AndreG-P/AGPKeebo/pcb/AGPKeeb.kicad_sch

## KiCad design pcb/AGPKeeb.kicad_sch (2023-09-22)

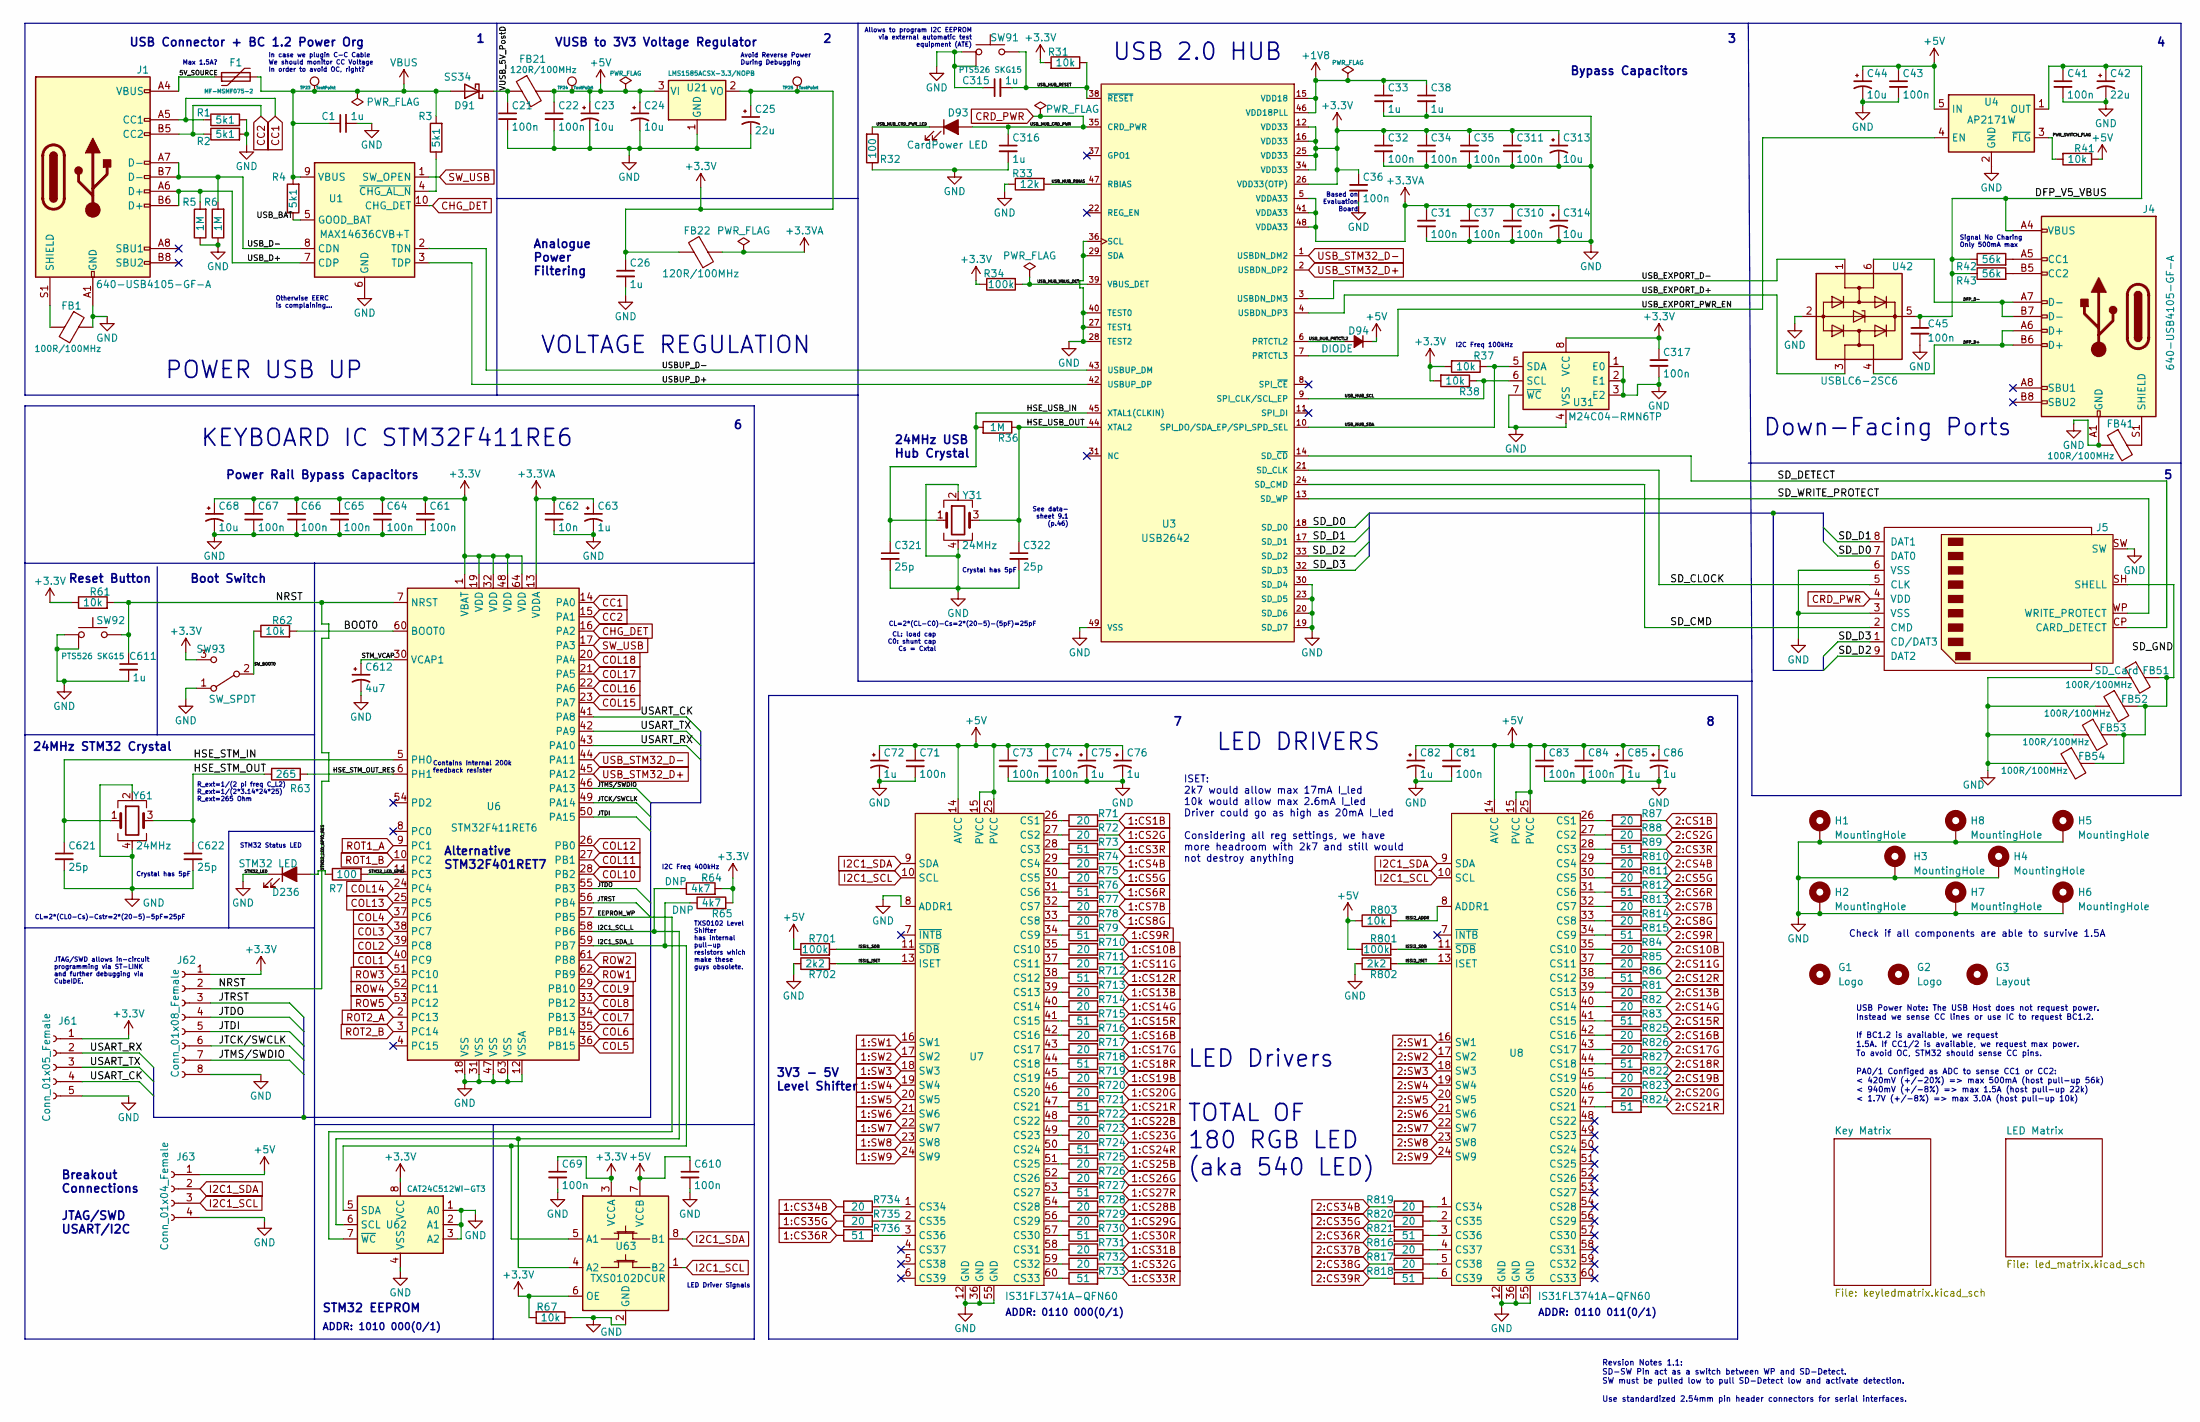
[picture p17: schematic AGPKeeb.kicad_sch]

Parts:
C1, C26, C33, C38, C63, C72, C75, C76, C82, C85, C86, C315, C316, C611: 1u; C_0402_1005Metric; LCSC C52923
C21, C22, C31, C32, C34, C35, C36, C37, C41, C43, C45, C61, C64, C65, C66, C67, C69, C71, C73, C74, C81, C83, C84, C310, C311, C317, C610: 100n; C_0402_1005Metric; LCSC C1525
C23, C24, C44, C68, C313, C314: 10u; CP_EIA-3216-18_Kemet-A; LCSC C7171
C25, C42: 22u; CP_EIA-3216-18_Kemet-A_Pad1.58x1.35mm_HandSolder
C62: 10n; C_0402_1005Metric; LCSC C15195
C321, C322, C621, C622: 25p; C_0603_1608Metric; LCSC C388042
C612: 4u7; CP_EIA-3216-18_Kemet-A_Pad1.58x1.35mm_HandSolder
D91: SS34; D_SMA; LCSC C8678
D93: CardPower LED; Fuse_0603_1608Metric
D94: DIODE; D_SOD-323; LCSC C191023
D236: STM32 LED; Fuse_0603_1608Metric
F1: MF-MSMF075-2; Fuse_1812_4532Metric
FB1, FB41, FB51, FB52, FB53, FB54: 100R/100MHz; L_0805_2012Metric_Pad1.05x1.20mm_HandSolder; LCSC C1015
FB21, FB22: 120R/100MHz; L_0603_1608Metric; LCSC *C113030
G1: Logo; agp-logo
G2: Logo; agp-logo-large
G3: Layout; layout
H1, H2, H3, H4, H5, H6, H7, H8: MountingHole; MountingHole_2.2mm_M2_Pad_Via
J1, J4: 640-USB4105-GF-A; USB_C_Receptacle_GCT_USB4105-xx-A_16P_TopMnt_Horizontal
J5: SD_Card; SD_Hirose_DM1AA_SF_PEJ82
J61: Conn_01x05_Female; JST_SH_SM05B-SRSS-TB_1x05-1MP_P1.00mm_Horizontal
J62: Conn_01x08_Female; JST_SH_SM08B-SRSS-TB_1x08-1MP_P1.00mm_Horizontal
J63: Conn_01x04_Female; JST_SH_SM04B-SRSS-TB_1x04-1MP_P1.00mm_Horizontal
R1, R2, R3, R4: 5k1; R_0402_1005Metric; LCSC C25905
R5, R6, R36: 1M; R_0402_1005Metric; LCSC C26083
R7, R32: 100; R_0402_1005Metric; LCSC C25076
R31, R37, R38, R41, R61, R62, R67, R803: 10k; R_0402_1005Metric; LCSC C25744
R33: 12k; R_0402_1005Metric; LCSC C25752
R34, R701, R801: 100k; R_0402_1005Metric; LCSC C25741
R42, R43: 56k; R_0402_1005Metric; LCSC C25796
R63: 265; R_0402_1005Metric; LCSC C11543
R64, R65: 4k7; R_0402_1005Metric
R71, R72, R74, R75, R77, R78, R81, R82, R84, R85, R87, R88, R710, R711, R713, R714, R716, R717, R719, R720, R722, R723, R725, R726, R728, R729, R731, R732, R734, R735, R810, R811, R813, R814, R816, R817, R819, R820, R822, R823, R825, R826: 20; R_0402_1005Metric; LCSC C25089
R73, R76, R79, R83, R86, R89, R712, R715, R718, R721, R724, R727, R730, R733, R736, R812, R815, R818, R821, R824, R827: 51; R_0402_1005Metric; LCSC C25125
R702, R802: 2k2; R_0402_1005Metric; LCSC C25879
SW91, SW92: PTS526 SKG15; SW_SPST_PTS526; LCSC *C2800943
SW93: SW_SPDT; SW_SPDT_PCM12; LCSC *C109335
TP23, TP24, TP25: TestPoint; TestPoint_Pad_D1.0mm
U1: MAX14636CVB+T; UTQFN-10_1.6x2.1mm_P0.5mm
U3: USB2642; Microchip_Technology-48QFN-5304-7x7B-07_2007-B-MFG
U4: AP2171W; SOT-23-5; LCSC *C110466
U6: STM32F411RET6; LQFP-64_10x10mm_P0.5mm; LCSC C94355
U7, U8: IS31FL3741A-QFN60; QFN-60-1EP_7x7mm_P0.4_EP5x5mm_ThermalVias; LCSC *C2940604
U21: LMS1585ACSX-3.3/NOPB; TO-252-3_TabPin2
U31: M24C04-RMN6TP; SOIC-8_3.9x4.9mm_P1.27mm; LCSC *C118280
U42: USBLC6-2SC6; SOT-23-6; LCSC *C2827654
U62: CAT24C512WI-GT3; SOIC-8_3.9x4.9mm_P1.27mm; LCSC *C79986
U63: TXS0102DCUR; VSSOP-8_2.3x2mm_P0.5mm; LCSC *C53434
Y31, Y61: 24MHz; Crystal_SMD_TXC_7M-4Pin_3.2x2.5mm; LCSC *C164048

Connections:
1:CS1B: R71.2
1:CS2G: R72.2
1:CS3R: R73.2
1:CS4B: R74.2
1:CS5G: R75.2
1:CS6R: R76.2
1:CS7B: R77.2
1:CS8G: R78.2
1:CS9R: R79.2
1:CS10B: R710.2
1:CS11G: R711.2
1:CS12R: R712.2
1:CS13B: R713.2
1:CS14G: R714.2
1:CS15R: R715.2
1:CS16B: R716.2
1:CS17G: R717.2
1:CS18R: R718.2
1:CS19B: R719.2
1:CS20G: R720.2
1:CS21R: R721.2
1:CS22B: R722.2
1:CS23G: R723.2
1:CS24R: R724.2
1:CS25B: R725.2
1:CS26G: R726.2
1:CS27R: R727.2
1:CS28B: R728.2
1:CS29G: R729.2
1:CS30R: R730.2
1:CS31B: R731.2
1:CS32G: R732.2
1:CS33R: R733.2
1:CS34B: R734.1
1:CS35G: R735.1
1:CS36R: R736.1
1:SW1: U7.16 (SW1)
1:SW2: U7.17 (SW2)
1:SW3: U7.18 (SW3)
1:SW4: U7.19 (SW4)
1:SW5: U7.20 (SW5)
1:SW6: U7.21 (SW6)
1:SW7: U7.22 (SW7)
1:SW8: U7.23 (SW8)
1:SW9: U7.24 (SW9)
2:CS1B: R87.2
2:CS2G: R88.2
2:CS3R: R89.2
2:CS4B: R810.2
2:CS5G: R811.2
2:CS6R: R812.2
2:CS7B: R813.2
2:CS8G: R814.2
2:CS9R: R815.2
2:CS10B: R84.2
2:CS11G: R85.2
2:CS12R: R86.2
2:CS13B: R81.2
2:CS14G: R82.2
2:CS15R: R83.2
2:CS16B: R825.2
2:CS17G: R826.2
2:CS18R: R827.2
2:CS19B: R822.2
2:CS20G: R823.2
2:CS21R: R824.2
2:CS34B: R819.2
2:CS35G: R820.2
2:CS36R: R821.2
2:CS37B: R816.2
2:CS38G: R817.2
2:CS39R: R818.2
2:SW1: U8.16 (SW1)
2:SW2: U8.17 (SW2)
2:SW3: U8.18 (SW3)
2:SW4: U8.19 (SW4)
2:SW5: U8.20 (SW5)
2:SW6: U8.21 (SW6)
2:SW7: U8.22 (SW7)
2:SW8: U8.23 (SW8)
2:SW9: U8.24 (SW9)
5V_SOURCE: F1.1, J1.A4 (VBUS), J1.A9 (VBUS), J1.B4 (VBUS), J1.B9 (VBUS)
+1V8: C33.1, C38.1, U3.15 (VDD18), U3.46 (VDD18PLL)
+3.3V: C25.1, C26.1, C32.1, C34.1, C35.1, C36.1, C61.1, C64.1, C65.1, C66.1, C67.1, C68.1, C69.1, C311.1, C313.1, C317.1, FB22.2, J61.1, J62.1, R31.2, R34.1, R37.2, R38.2, R61.1, R64.2, R65.2, R67.2, SW93.3 (C), TP25.1, U3.12 (VDD33), U3.16 (VDD33), U3.25 (VDD33), U3.26 (VDD33(OTP)), U3.34 (VDD33), U6.1 (VBAT), U6.19 (VDD), U6.32 (VDD), U6.48 (VDD), U6.64 (VDD), U21.2 (VO), U31.8 (VCC), U62.8 (VCC), U63.3 (VCCA), U63.6 (OE)
+3.3VA: C31.1, C37.1, C62.1, C63.1, C310.1, C314.1, FB22.1, U3.5 (VDDA33), U3.41 (VDDA33), U3.48 (VDDA33), U6.13 (VDDA)
+5V: C22.1, C23.1, C24.1, C43.1, C44.1, C71.1, C72.1, C73.1, C74.1, C75.1, C76.1, C81.1, C82.1, C83.1, C84.1, C85.1, C86.1, C610.1, D94.1 (K), FB21.2, J63.1, R41.1, R701.1, R801.1, R803.1, TP24.1, U4.5 (IN), U7.14 (AVCC), U7.15 (PVCC), U7.25 (PVCC), U8.14 (AVCC), U8.15 (PVCC), U8.25 (PVCC), U21.3 (VI), U63.7 (VCCB)
BOOT0: R62.2, U6.60 (BOOT0)
CC1: J1.A5 (CC1), R1.1, U6.14 (PA0)
CC2: J1.B5 (CC2), R2.1, U6.15 (PA1)
CHG_DET: U1.10 (CHG_DET), U6.16 (PA2)
COL1: U6.40 (PC9)
COL2: U6.39 (PC8)
COL3: U6.38 (PC7)
COL4: U6.37 (PC6)
COL5: U6.36 (PB15)
COL6: U6.35 (PB14)
COL7: U6.34 (PB13)
COL8: U6.33 (PB12)
COL9: U6.29 (PB10)
COL10: U6.28 (PB2)
COL11: U6.27 (PB1)
COL12: U6.26 (PB0)
COL13: U6.25 (PC5)
COL14: U6.24 (PC4)
COL15: U6.23 (PA7)
COL16: U6.22 (PA6)
COL17: U6.21 (PA5)
COL18: U6.20 (PA4)
CRD_PWR: C316.1, D93.2 (A), J5.4 (VDD), U3.35 (CRD_PWR)
DFP_D+: J4.A6 (D+), J4.B6 (D+), U42.4 (I/O2)
DFP_D-: J4.A7 (D-), J4.B7 (D-), U42.6 (I/O1)
DFP_V5_VBUS: C41.1, C42.1, C45.1, J4.A4 (VBUS), J4.A9 (VBUS), J4.B4 (VBUS), J4.B9 (VBUS), R42.1, R43.1, U4.1 (OUT), U42.5 (VBUS)
EEPROM_WP: U6.57 (PB5), U62.7 (~WC)
GND: C1.2, C21.2, C22.2, C23.2, C24.2, C25.2, C26.2, C31.2, C32.2, C33.2, C34.2, C35.2, C36.2, C37.2, C38.2, C41.2, C42.2, C43.2, C44.2, C45.2, C61.2, C62.2, C63.2, C64.2, C65.2, C66.2, C67.2, C68.2, C69.2, C71.2, C72.2, C73.2, C74.2, C75.2, C76.2, C81.2, C82.2, C83.2, C84.2, C85.2, C86.2, C310.2, C311.2, C313.2, C314.2, C315.1, C316.2, C317.2, C321.2, C322.2, C610.2, C611.2, C612.2, C621.2, C622.2, D236.1 (K), FB1.1, FB41.1, FB51.1, FB52.1, FB53.1, FB54.1, H1.1, H2.1, H3.1, H4.1, H5.1, H6.1, H7.1, H8.1, J1.A1 (GND), J1.A12 (GND), J1.B1 (GND), J1.B12 (GND), J4.A1 (GND), J4.A12 (GND), J4.B1 (GND), J4.B12 (GND), J5.3 (VSS), J5.6 (VSS), J5.SW, J61.5, J62.8, J63.4, R1.2, R2.2, R5.1, R6.1, R32.1, R33.1, R67.1, R702.1, R802.1, SW91.1, SW91.3 (GND), SW92.1, SW92.3 (GND), SW93.1 (A), U1.6 (GND), U3.19 (SD_D7), U3.20 (SD_D6), U3.23 (SD_D5), U3.27 (TEST1), U3.28 (TEST2), U3.29 (SDA), U3.30 (SD_D4), U3.36 (SCL), U3.40 (TEST0), U3.49 (VSS), U4.2 (GND), U6.12 (VSSA), U6.18 (VSS), U6.31 (VSS), U6.47 (VSS), U6.63 (VSS), U7.8 (ADDR1), U7.12 (GND), U7.36 (GND), U7.55 (GND), U7.61 (PGND), U8.12 (GND), U8.36 (GND), U8.55 (GND), U8.61 (PGND), U21.1 (GND), U31.1 (E0), U31.2 (E1), U31.3 (E2), U31.4 (VSS), U31.7 (~WC), U42.2 (GND), U62.1 (A0), U62.2 (A1), U62.3 (A2), U62.4 (VSS), U63.2 (GND), Y31.2, Y31.4, Y61.2, Y61.4
HSE_STM_IN: C621.1, U6.5 (PH0), Y61.1
HSE_STM_OUT: C622.1, R63.1, Y61.3
HSE_STM_OUT_RES: R63.2, U6.6 (PH1)
HSE_USB_IN: C321.1, R36.2, U3.45 (XTAL1(CLKIN)), Y31.1
HSE_USB_OUT: C322.1, R36.1, U3.44 (XTAL2), Y31.3
I2C1_SCL: J63.3, U7.10 (SCL), U8.10 (SCL), U63.1 (B2)
I2C1_SCL_L: R64.1, U6.58 (PB6), U62.6 (SCL), U63.4 (A2)
I2C1_SDA: J63.2, U7.9 (SDA), U8.9 (SDA), U63.8 (B1)
I2C1_SDA_L: R65.1, U6.59 (PB7), U62.5 (SDA), U63.5 (A1)
ISSI1_ISET: R702.2, U7.13 (ISET)
ISSI1_SDB: R701.2, U7.11 (~SDB)
ISSI2_ADDR: R803.2, U8.8 (ADDR1)
ISSI2_ISET: R802.2, U8.13 (ISET)
ISSI2_SDB: R801.2, U8.11 (~SDB)
JTCK/SWCLK: J62.6, U6.49 (PA14)
JTDI: J62.5, U6.50 (PA15)
JTDO: J62.4, U6.55 (PB3)
JTMS/SWDIO: J62.7, U6.46 (PA13)
JTRST: J62.3, U6.56 (PB4)
NRST: C611.1, J62.2, R61.2, SW92.2, U6.7 (NRST)
unnamed: FB1.2, J1.S1 (SHIELD)
unnamed: FB41.2, J4.S1 (SHIELD)
unnamed: J4.A5 (CC1), R42.2
unnamed: J4.B5 (CC2), R43.2
unnamed: R3.1, U1.4 (~CHG_AL_N)
unnamed: R71.1, U7.26 (CS1)
unnamed: R72.1, U7.27 (CS2)
unnamed: R73.1, U7.28 (CS3)
unnamed: R74.1, U7.29 (CS4)
unnamed: R75.1, U7.30 (CS5)
unnamed: R76.1, U7.31 (CS6)
unnamed: R77.1, U7.32 (CS7)
unnamed: R78.1, U7.33 (CS8)
unnamed: R79.1, U7.34 (CS9)
unnamed: R81.1, U8.39 (CS13)
unnamed: R82.1, U8.40 (CS14)
unnamed: R83.1, U8.41 (CS15)
unnamed: R84.1, U8.35 (CS10)
unnamed: R85.1, U8.37 (CS11)
unnamed: R86.1, U8.38 (CS12)
unnamed: R87.1, U8.26 (CS1)
unnamed: R88.1, U8.27 (CS2)
unnamed: R89.1, U8.28 (CS3)
unnamed: R710.1, U7.35 (CS10)
unnamed: R711.1, U7.37 (CS11)
unnamed: R712.1, U7.38 (CS12)
unnamed: R713.1, U7.39 (CS13)
unnamed: R714.1, U7.40 (CS14)
unnamed: R715.1, U7.41 (CS15)
unnamed: R716.1, U7.42 (CS16)
unnamed: R717.1, U7.43 (CS17)
unnamed: R718.1, U7.44 (CS18)
unnamed: R719.1, U7.45 (CS19)
unnamed: R720.1, U7.46 (CS20)
unnamed: R721.1, U7.47 (CS21)
unnamed: R722.1, U7.48 (CS22)
unnamed: R723.1, U7.49 (CS23)
unnamed: R724.1, U7.50 (CS24)
unnamed: R725.1, U7.51 (CS25)
unnamed: R726.1, U7.52 (CS26)
unnamed: R727.1, U7.53 (CS27)
unnamed: R728.1, U7.54 (CS28)
unnamed: R729.1, U7.56 (CS29)
unnamed: R730.1, U7.57 (CS30)
unnamed: R731.1, U7.58 (CS31)
unnamed: R732.1, U7.59 (CS32)
unnamed: R733.1, U7.60 (CS33)
unnamed: R734.2, U7.1 (CS34)
unnamed: R735.2, U7.2 (CS35)
unnamed: R736.2, U7.3 (CS36)
unnamed: R810.1, U8.29 (CS4)
unnamed: R811.1, U8.30 (CS5)
unnamed: R812.1, U8.31 (CS6)
unnamed: R813.1, U8.32 (CS7)
unnamed: R814.1, U8.33 (CS8)
unnamed: R815.1, U8.34 (CS9)
unnamed: R816.1, U8.4 (CS37)
unnamed: R817.1, U8.5 (CS38)
unnamed: R818.1, U8.6 (CS39)
unnamed: R819.1, U8.1 (CS34)
unnamed: R820.1, U8.2 (CS35)
unnamed: R821.1, U8.3 (CS36)
unnamed: R822.1, U8.45 (CS19)
unnamed: R823.1, U8.46 (CS20)
unnamed: R824.1, U8.47 (CS21)
unnamed: R825.1, U8.42 (CS16)
unnamed: R826.1, U8.43 (CS17)
unnamed: R827.1, U8.44 (CS18)
PWR_SWITCH_FLAG: R41.2, U4.3 (~FLG)
ROT1_A: U6.9 (PC1)
ROT1_B: U6.10 (PC2)
ROT2_A: U6.2 (PC13)
ROT2_B: U6.3 (PC14)
ROW1: U6.62 (PB9)
ROW2: U6.61 (PB8)
ROW3: U6.51 (PC10)
ROW4: U6.52 (PC11)
ROW5: U6.53 (PC12)
SD_CLOCK: J5.5 (CLK), U3.21 (SD_CLK)
SD_CMD: J5.2 (CMD), U3.24 (SD_CMD)
SD_D0: J5.7 (DAT0), U3.18 (SD_D0)
SD_D1: J5.8 (DAT1), U3.17 (SD_D1)
SD_D2: J5.9 (DAT2), U3.33 (SD_D2)
SD_D3: J5.1 (CD/DAT3), U3.32 (SD_D3)
SD_DETECT: J5.CP (CARD_DETECT), U3.14 (SD_~CD)
SD_GND: FB51.2, FB52.2, FB53.2, FB54.2, J5.SH (SHELL)
SD_WRITE_PROTECT: J5.WP (WRITE_PROTECT), U3.13 (SD_WP)
STM32_LED_GPIO: R7.2, U6.11 (PC3)
STM32_LED_GPIO_RES: D236.2 (A), R7.1
STM_VCAP: C612.1, U6.30 (VCAP1)
SW_BOOT0: R62.1, SW93.2 (B)
SW_USB: U1.1 (SW_OPEN), U6.17 (PA3)
USART_CK: J61.4, U6.41 (PA8)
USART_RX: J61.2, U6.43 (PA10)
USART_TX: J61.3, U6.42 (PA9)
USBUP_D+: U1.3 (TDP), U3.42 (USBUP_DP)
USBUP_D-: U1.2 (TDN), U3.43 (USBUP_DM)
USB_BAT: R4.1, U1.5 (GOOD_BAT)
USB_D+: J1.A6 (D+), J1.B6 (D+), R5.2, U1.7 (CDP)
USB_D-: J1.A7 (D-), J1.B7 (D-), R6.2, U1.8 (CDN)
USB_EXPORT_D+: U3.4 (USBDN_DP3), U42.3 (I/O2)
USB_EXPORT_D-: U3.3 (USBDN_DM3), U42.1 (I/O1)
USB_EXPORT_PWR_EN: U3.7 (PRTCTL3), U4.4 (EN)
USB_HUB_CRD_PWR_LED: D93.1 (K), R32.2
USB_HUB_PRTCTL2: D94.2 (A), U3.6 (PRTCTL2)
USB_HUB_RBIAS: R33.2, U3.47 (RBIAS)
USB_HUB_RESET: C315.2, R31.1, SW91.2, U3.38 (~RESET)
USB_HUB_SCL: R38.1, U3.9 (SPI_CLK/SCL_EP), U31.6 (SCL)
USB_HUB_SDA: R37.1, U3.10 (SPI_DO/SDA_EP/SPI_SPD_SEL), U31.5 (SDA)
USB_HUB_VBUS_DET: R34.2, U3.39 (VBUS_DET)
USB_STM32_D+: U3.2 (USBDN_DP2), U6.45 (PA12)
USB_STM32_D-: U3.1 (USBDN_DM2), U6.44 (PA11)
VBUS: C1.1, D91.2 (A), F1.2, R3.2, R4.2, TP23.1, U1.9 (VBUS)
VUSB_5V_PostD: C21.1, D91.1 (K), FB21.1

Notes on the sheet:
Boot Switch
Contains Internal 200k feedback resister
I2C Freq 100kHz
Crystal has 5pF
LED Driver Signals
JTAG/SWD allows in-circuit programming via ST-LINK and further debugging via CubeIDE.
VUSB to 3V3 Voltage Regulator
3V3 - 5V Level Shifter
In case we plugin C-C Cable We should monitor CC Voltage In order to avoid OC, right?
CL=2*(CL0-Cs)-Cstr=2*(20-5)-5pF=25pF
ADDR: 1010 000(0/1)
24MHz USB Hub Crystal
ADDR: 0110 000(0/1)
CL: load cap C0: shunt cap Cs = Cxtal
Reset Button
VOLTAGE REGULATION
Max 1.5A?
Breakout Connections JTAG/SWD USART/I2C
TXS0102 Level Shifter has internal pull-up resistors which make these guys obsolete.
CL=2*(CL-C0)-Cs=2*(20-5)-(5pF)=25pF
ISET: 2k7 would allow max 17mA I_led 10k would allow max 2.6mA I_led Driver could go as high as 20mA I_led Considering all reg settings, we have more headroom with 2k7 and still would not destroy anything
STM32 EEPROM
I2C Freq 400kHz
Power Rail Bypass Capacitors
Bypass Capacitors
24MHz STM32 Crystal
KEYBOARD IC STM32F411RE6
Analogue Power Filtering
See data- sheet 9.1 (p.46)
ADDR: 0110 011(0/1)
USB 2.0 HUB
USB Connector + BC 1.2 Power Org
Down-Facing Ports
Revsion Notes 1.1: SD-SW Pin act as a switch between WP and SD-Detect. SW must be pulled low to pull SD-Detect low and activate detection. Use standardized 2.54mm pin header connectors for serial interfaces.
Check if all components are able to survive 1.5A
R_ext=1/(2 pi freq C_L2) R_ext=1/(2*3.14*24*25) R_ext=265 Ohm
Avoid Reverse Power During Debugging
STM32 Status LED
Signal No Charing Only 500mA max
LED DRIVERS
Alternative STM32F401RET7
POWER USB UP
USB Power Note: The USB Host does not request power. Instead we sense CC lines or use IC to request BC1.2. If BC1.2 is available, we request 1.5A. If CC1/2 is available, we request max power. To avoid OC, STM32 should sense CC pins. PA0/1 Configed as ADC to sense CC1 or CC2: < 420mV (+/-20%) => max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
LED Drivers TOTAL OF 180 RGB LED (aka 540 LED)
Allows to program I2C EEPROM via external automatic test equipment (ATE)
Otherwise EERC is complaining...
Based on Evaluation Board
