AndreG-P/AGPKeebo/pcb/keyledmatrix.kicad_sch

## KiCad design pcb/keyledmatrix.kicad_sch (2023-09-22)

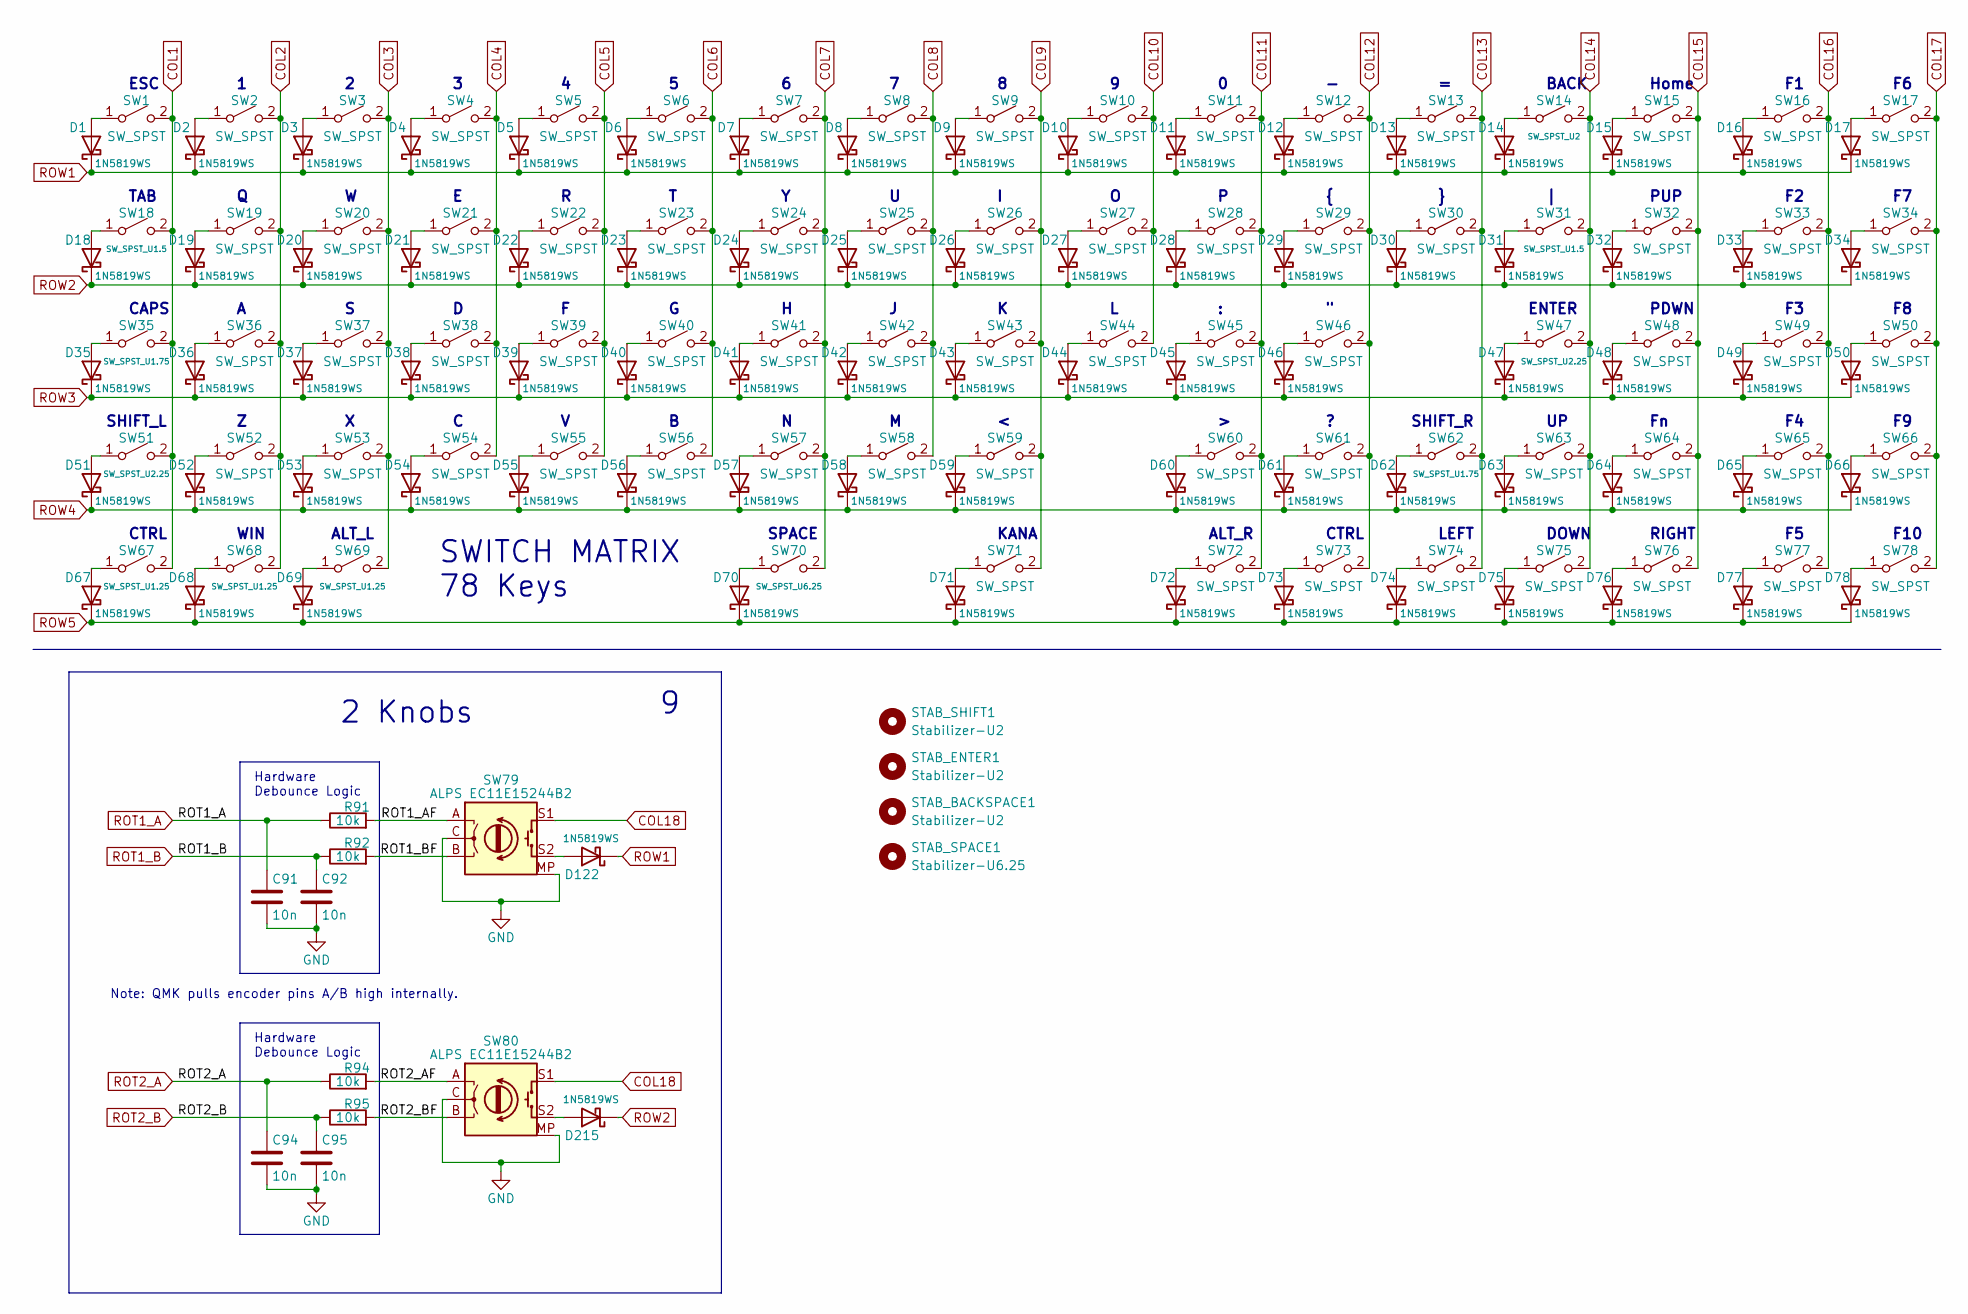
[picture p18: schematic keyledmatrix.kicad_sch]

Parts:
C91, C92, C94, C95: 10n; C_0402_1005Metric; LCSC C15195
D1, D2, D3, D4, D5, D6, D7, D8, D9, D10, D11, D12, D13, D14, D15, D16, D17, D18, D19, D20, D21, D22, D23, D24, D25, D26, D27, D28, D29, D30, D31, D32, D33, D34, D35, D36, D37, D38, D39, D40, D41, D42, D43, D44, D45, D46, D47, D48, D49, D50, D51, D52, D53, D54, D55, D56, D57, D58, D59, D60, D61, D62, D63, D64, D65, D66, D67, D68, D69, D70, D71, D72, D73, D74, D75, D76, D77, D78, D122, D215: 1N5819WS; D_SOD-323; LCSC C191023
R91, R92, R94, R95: 10k; R_0402_1005Metric; LCSC C25744
STAB_BACKSPACE1: Stabilizer-U2; Stabilizer_Cherry_MX_2.00u
STAB_ENTER1: Stabilizer-U2; Stabilizer_Cherry_MX_2.00u
STAB_SHIFT1: Stabilizer-U2; Stabilizer_Cherry_MX_2.00u
STAB_SPACE1: Stabilizer-U6.25; Stabilizer_Cherry_MX_6.25u
SW1, SW2, SW3, SW4, SW5, SW6, SW7, SW8, SW9, SW10, SW11, SW12, SW13, SW15, SW16, SW17, SW19, SW20, SW21, SW22, SW23, SW24, SW25, SW26, SW27, SW28, SW29, SW30, SW32, SW33, SW34, SW36, SW37, SW38, SW39, SW40, SW41, SW42, SW43, SW44, SW45, SW46, SW48, SW49, SW50, SW52, SW53, SW54, SW55, SW56, SW57, SW58, SW59, SW60, SW61, SW63, SW64, SW65, SW66, SW71, SW72, SW73, SW74, SW75, SW76, SW77, SW78: SW_SPST; SW_Hotswap_Kailh_MX_plated_1.00u_clear
SW14: SW_SPST_U2; SW_Hotswap_Kailh_MX_plated_2.00u_clear
SW18, SW31: SW_SPST_U1.5; SW_Hotswap_Kailh_MX_plated_1.50u_clear
SW35, SW62: SW_SPST_U1.75; SW_Hotswap_Kailh_MX_plated_1.75u_clear
SW47, SW51: SW_SPST_U2.25; SW_Hotswap_Kailh_MX_plated_2.25u_clear
SW67, SW68, SW69: SW_SPST_U1.25; SW_Hotswap_Kailh_MX_plated_1.25u_clear
SW70: SW_SPST_U6.25; SW_Hotswap_Kailh_MX_plated_6.25u_clear
SW79, SW80: ALPS EC11E15244B2; RotaryEncoder_Alps_EC11E-Switch_Vertical_H20mm; LCSC *C470754

Connections:
COL1: SW1.2 (B), SW18.2 (B), SW35.2 (B), SW51.2 (B), SW67.2 (B)
COL2: SW2.2 (B), SW19.2 (B), SW36.2 (B), SW52.2 (B), SW68.2 (B)
COL3: SW3.2 (B), SW20.2 (B), SW37.2 (B), SW53.2 (B), SW69.2 (B)
COL4: SW4.2 (B), SW21.2 (B), SW38.2 (B), SW54.2 (B)
COL5: SW5.2 (B), SW22.2 (B), SW39.2 (B), SW55.2 (B)
COL6: SW6.2 (B), SW23.2 (B), SW40.2 (B), SW56.2 (B)
COL7: SW7.2 (B), SW24.2 (B), SW41.2 (B), SW57.2 (B), SW70.2 (B)
COL8: SW8.2 (B), SW25.2 (B), SW42.2 (B), SW58.2 (B)
COL9: SW9.2 (B), SW26.2 (B), SW43.2 (B), SW59.2 (B), SW71.2 (B)
COL10: SW10.2 (B), SW27.2 (B), SW44.2 (B)
COL11: SW11.2 (B), SW28.2 (B), SW45.2 (B), SW60.2 (B), SW72.2 (B)
COL12: SW12.2 (B), SW29.2 (B), SW46.2 (B), SW61.2 (B), SW73.2 (B)
COL13: SW13.2 (B), SW30.2 (B), SW62.2 (B), SW74.2 (B)
COL14: SW14.2 (B), SW31.2 (B), SW47.2 (B), SW63.2 (B), SW75.2 (B)
COL15: SW15.2 (B), SW32.2 (B), SW48.2 (B), SW64.2 (B), SW76.2 (B)
COL16: SW16.2 (B), SW33.2 (B), SW49.2 (B), SW65.2 (B), SW77.2 (B)
COL17: SW17.2 (B), SW34.2 (B), SW50.2 (B), SW66.2 (B), SW78.2 (B)
COL18: SW79.S1, SW80.S1
GND: C91.2, C92.2, C94.2, C95.2, SW79.C, SW79.MP (Shell), SW80.C, SW80.MP (Shell)
unnamed: D1.2 (A), SW1.1 (A)
unnamed: D2.2 (A), SW2.1 (A)
unnamed: D3.2 (A), SW3.1 (A)
unnamed: D4.2 (A), SW4.1 (A)
unnamed: D5.2 (A), SW5.1 (A)
unnamed: D6.2 (A), SW6.1 (A)
unnamed: D7.2 (A), SW7.1 (A)
unnamed: D8.2 (A), SW8.1 (A)
unnamed: D9.2 (A), SW9.1 (A)
unnamed: D10.2 (A), SW10.1 (A)
unnamed: D11.2 (A), SW11.1 (A)
unnamed: D12.2 (A), SW12.1 (A)
unnamed: D13.2 (A), SW13.1 (A)
unnamed: D14.2 (A), SW14.1 (A)
unnamed: D15.2 (A), SW15.1 (A)
unnamed: D16.2 (A), SW16.1 (A)
unnamed: D17.2 (A), SW17.1 (A)
unnamed: D18.2 (A), SW18.1 (A)
unnamed: D19.2 (A), SW19.1 (A)
unnamed: D20.2 (A), SW20.1 (A)
unnamed: D21.2 (A), SW21.1 (A)
unnamed: D22.2 (A), SW22.1 (A)
unnamed: D23.2 (A), SW23.1 (A)
unnamed: D24.2 (A), SW24.1 (A)
unnamed: D25.2 (A), SW25.1 (A)
unnamed: D26.2 (A), SW26.1 (A)
unnamed: D27.2 (A), SW27.1 (A)
unnamed: D28.2 (A), SW28.1 (A)
unnamed: D29.2 (A), SW29.1 (A)
unnamed: D30.2 (A), SW30.1 (A)
unnamed: D31.2 (A), SW31.1 (A)
unnamed: D32.2 (A), SW32.1 (A)
unnamed: D33.2 (A), SW33.1 (A)
unnamed: D34.2 (A), SW34.1 (A)
unnamed: D35.2 (A), SW35.1 (A)
unnamed: D36.2 (A), SW36.1 (A)
unnamed: D37.2 (A), SW37.1 (A)
unnamed: D38.2 (A), SW38.1 (A)
unnamed: D39.2 (A), SW39.1 (A)
unnamed: D40.2 (A), SW40.1 (A)
unnamed: D41.2 (A), SW41.1 (A)
unnamed: D42.2 (A), SW42.1 (A)
unnamed: D43.2 (A), SW43.1 (A)
unnamed: D44.2 (A), SW44.1 (A)
unnamed: D45.2 (A), SW45.1 (A)
unnamed: D46.2 (A), SW46.1 (A)
unnamed: D47.2 (A), SW47.1 (A)
unnamed: D48.2 (A), SW48.1 (A)
unnamed: D49.2 (A), SW49.1 (A)
unnamed: D50.2 (A), SW50.1 (A)
unnamed: D51.2 (A), SW51.1 (A)
unnamed: D52.2 (A), SW52.1 (A)
unnamed: D53.2 (A), SW53.1 (A)
unnamed: D54.2 (A), SW54.1 (A)
unnamed: D55.2 (A), SW55.1 (A)
unnamed: D56.2 (A), SW56.1 (A)
unnamed: D57.2 (A), SW57.1 (A)
unnamed: D58.2 (A), SW58.1 (A)
unnamed: D59.2 (A), SW59.1 (A)
unnamed: D60.2 (A), SW60.1 (A)
unnamed: D61.2 (A), SW61.1 (A)
unnamed: D62.2 (A), SW62.1 (A)
unnamed: D63.2 (A), SW63.1 (A)
unnamed: D64.2 (A), SW64.1 (A)
unnamed: D65.2 (A), SW65.1 (A)
unnamed: D66.2 (A), SW66.1 (A)
unnamed: D67.2 (A), SW67.1 (A)
unnamed: D68.2 (A), SW68.1 (A)
unnamed: D69.2 (A), SW69.1 (A)
unnamed: D70.2 (A), SW70.1 (A)
unnamed: D71.2 (A), SW71.1 (A)
unnamed: D72.2 (A), SW72.1 (A)
unnamed: D73.2 (A), SW73.1 (A)
unnamed: D74.2 (A), SW74.1 (A)
unnamed: D75.2 (A), SW75.1 (A)
unnamed: D76.2 (A), SW76.1 (A)
unnamed: D77.2 (A), SW77.1 (A)
unnamed: D78.2 (A), SW78.1 (A)
unnamed: D122.2 (A), SW79.S2
unnamed: D215.2 (A), SW80.S2
ROT1_A: C91.1, R91.1
ROT1_AF: R91.2, SW79.A
ROT1_B: C92.1, R92.1
ROT1_BF: R92.2, SW79.B
ROT2_A: C94.1, R94.1
ROT2_AF: R94.2, SW80.A
ROT2_B: C95.1, R95.1
ROT2_BF: R95.2, SW80.B
ROW1: D1.1 (K), D2.1 (K), D3.1 (K), D4.1 (K), D5.1 (K), D6.1 (K), D7.1 (K), D8.1 (K), D9.1 (K), D10.1 (K), D11.1 (K), D12.1 (K), D13.1 (K), D14.1 (K), D15.1 (K), D16.1 (K), D17.1 (K), D122.1 (K)
ROW2: D18.1 (K), D19.1 (K), D20.1 (K), D21.1 (K), D22.1 (K), D23.1 (K), D24.1 (K), D25.1 (K), D26.1 (K), D27.1 (K), D28.1 (K), D29.1 (K), D30.1 (K), D31.1 (K), D32.1 (K), D33.1 (K), D34.1 (K), D215.1 (K)
ROW3: D35.1 (K), D36.1 (K), D37.1 (K), D38.1 (K), D39.1 (K), D40.1 (K), D41.1 (K), D42.1 (K), D43.1 (K), D44.1 (K), D45.1 (K), D46.1 (K), D47.1 (K), D48.1 (K), D49.1 (K), D50.1 (K)
ROW4: D51.1 (K), D52.1 (K), D53.1 (K), D54.1 (K), D55.1 (K), D56.1 (K), D57.1 (K), D58.1 (K), D59.1 (K), D60.1 (K), D61.1 (K), D62.1 (K), D63.1 (K), D64.1 (K), D65.1 (K), D66.1 (K)
ROW5: D67.1 (K), D68.1 (K), D69.1 (K), D70.1 (K), D71.1 (K), D72.1 (K), D73.1 (K), D74.1 (K), D75.1 (K), D76.1 (K), D77.1 (K), D78.1 (K)

Notes on the sheet:
F10
LEFT
SWITCH MATRIX 78 Keys
SHIFT_R
BACK
ALT_L
TAB
Hardware Debounce Logic
CTRL
SHIFT_L
KANA
PDWN
ENTER
Note: QMK pulls encoder pins A/B high internally.
CAPS
WIN
2 Knobs
SPACE
Home
DOWN
ALT_R
RIGHT
PUP
ESC
