AndreG-P/AGPKeebo/pcb/led_matrix.kicad_sch

## KiCad design pcb/led_matrix.kicad_sch (2023-09-22)

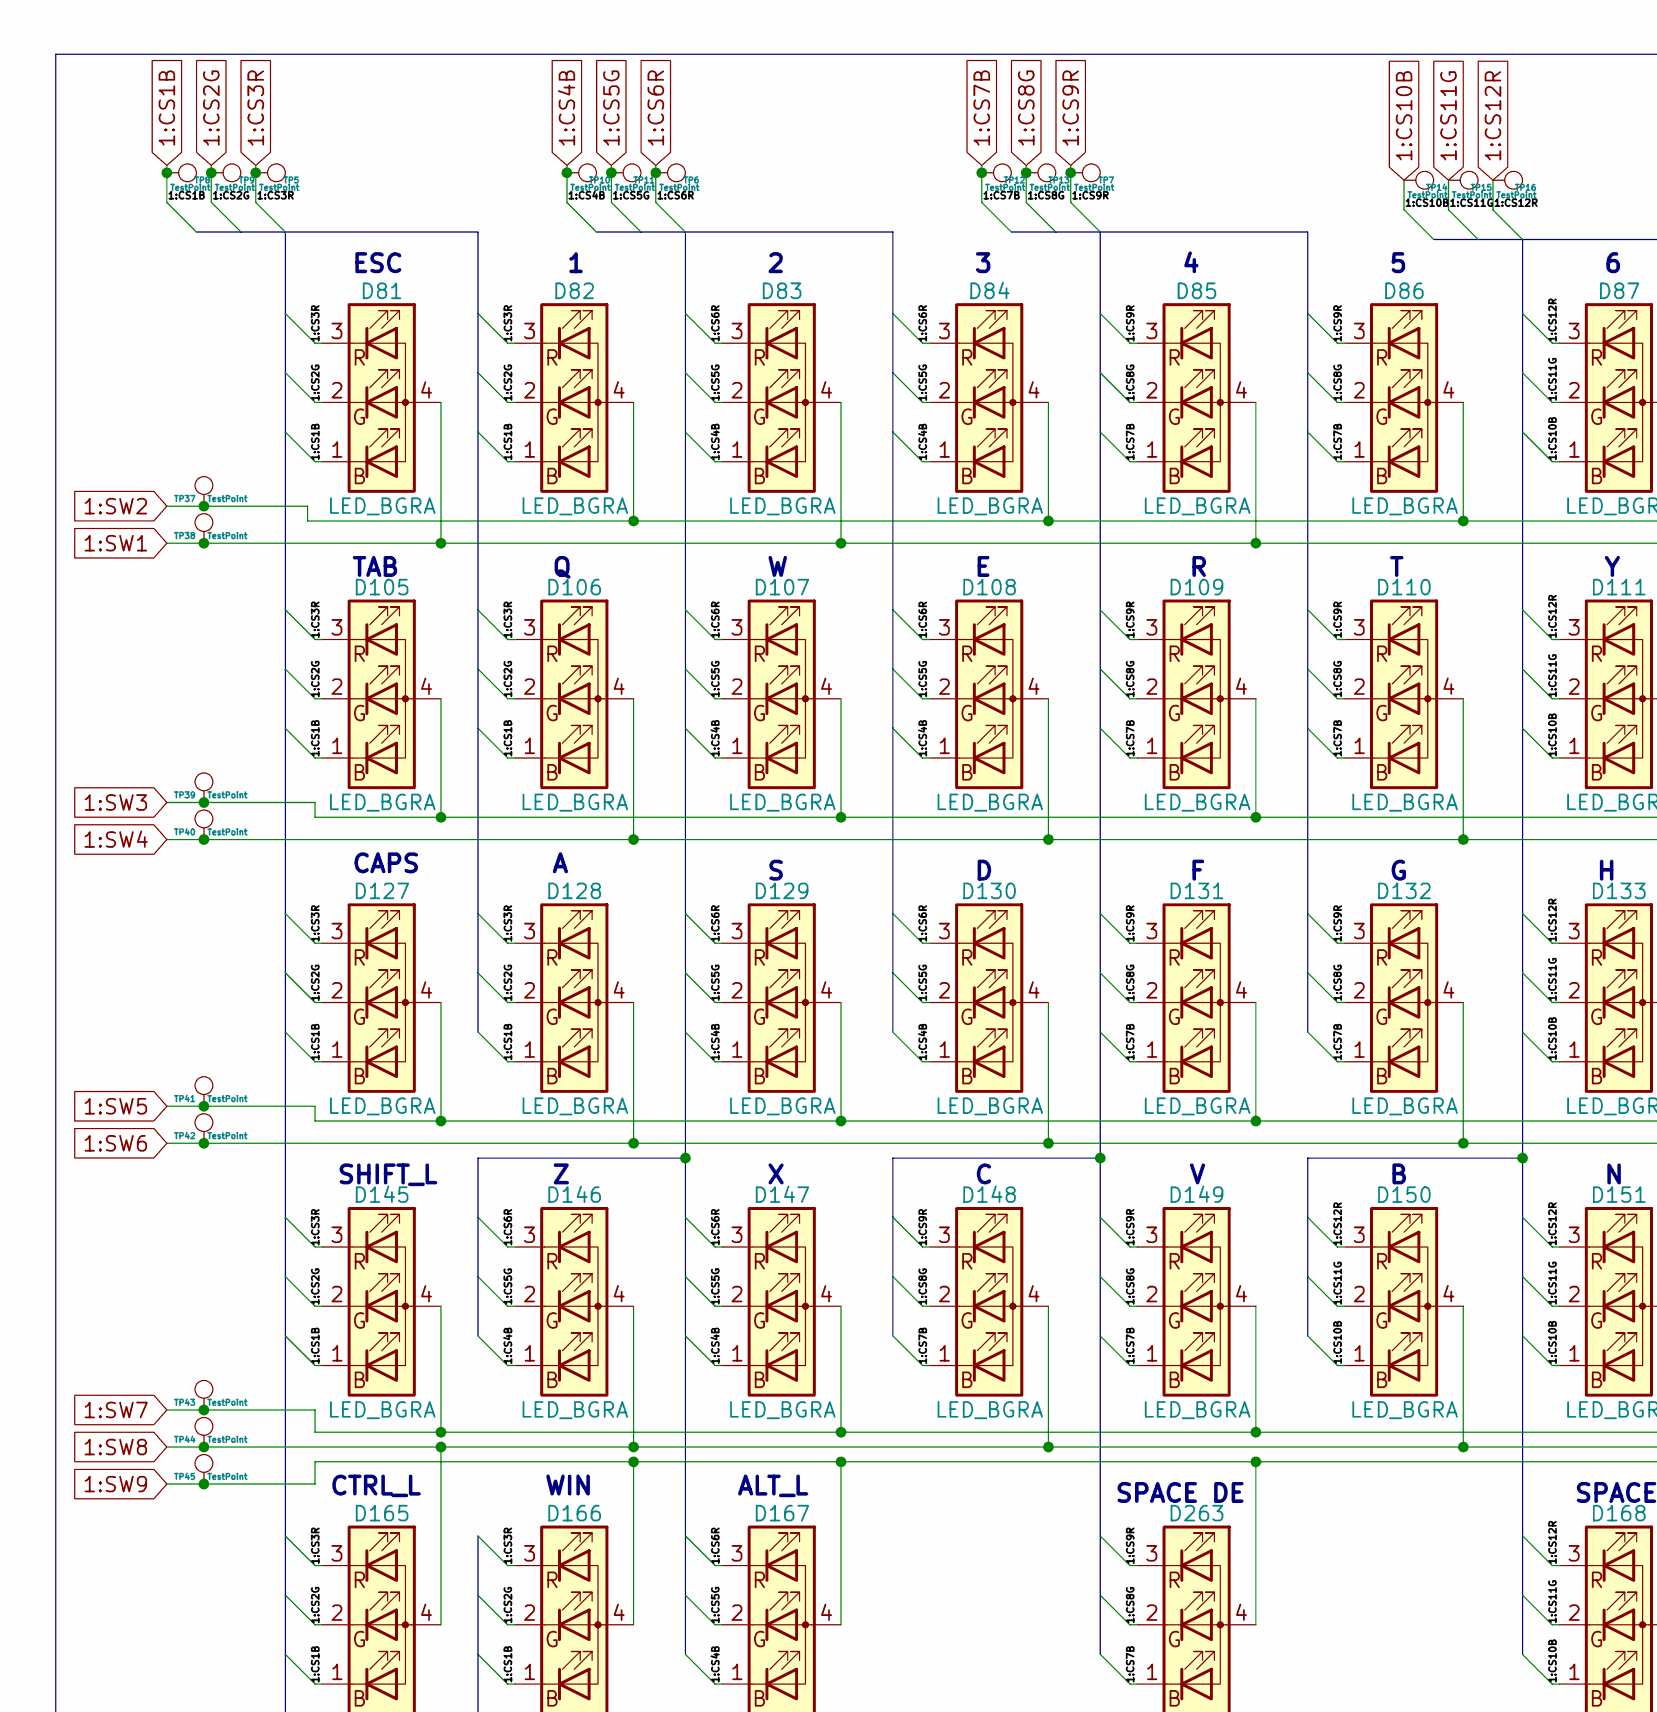
[picture p19: schematic led_matrix.kicad_sch, part in row 1, column 1]

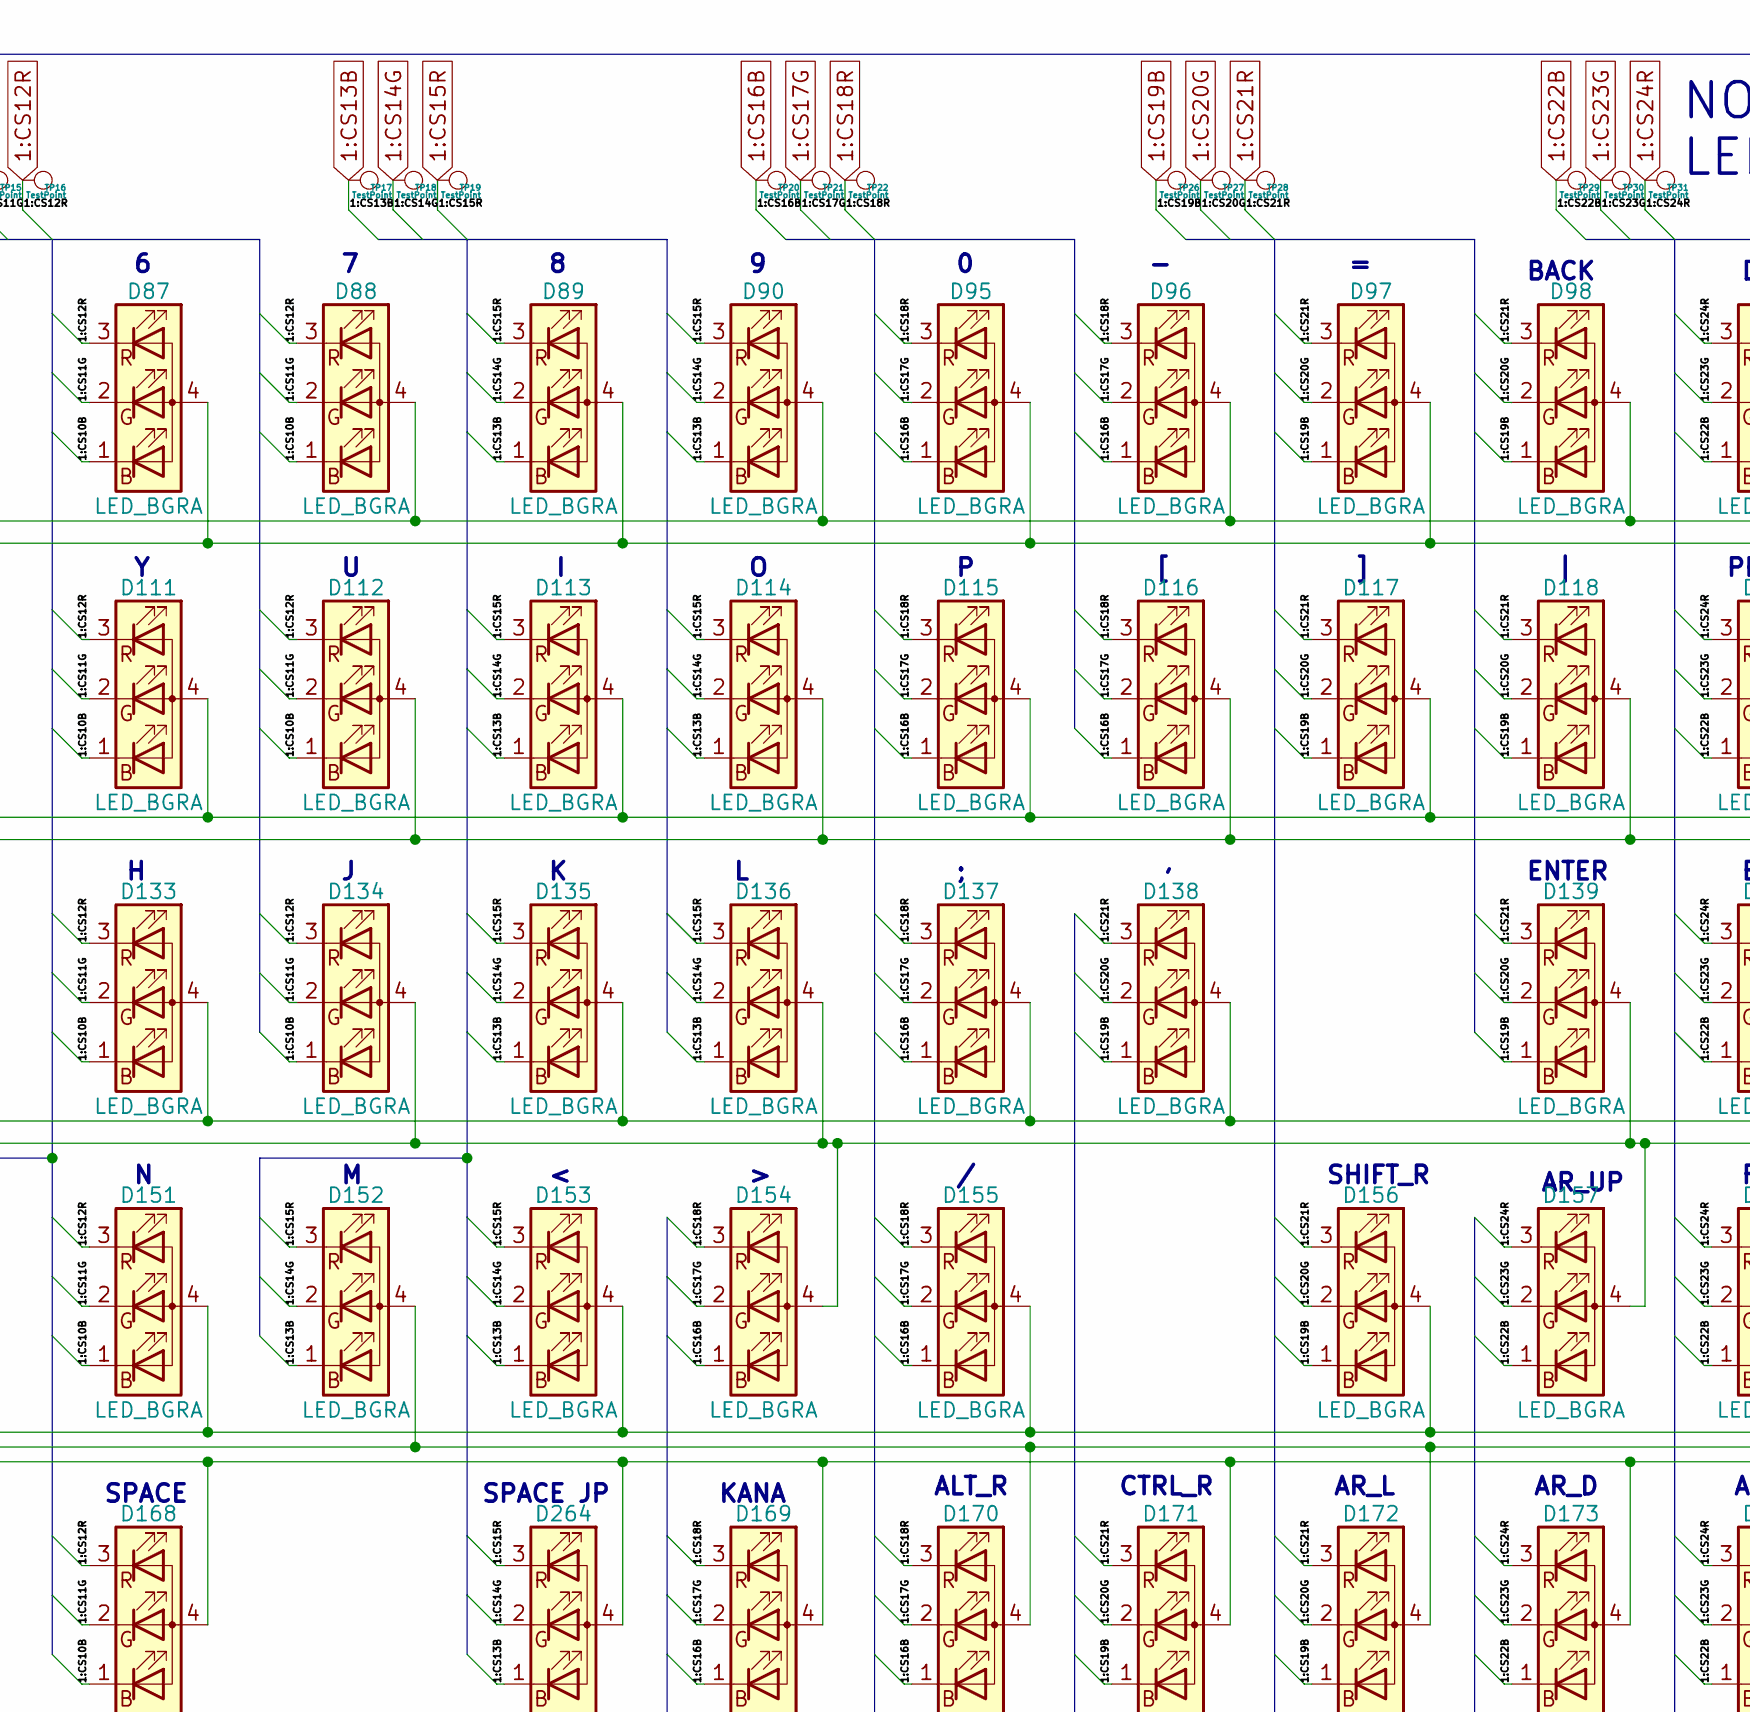
[picture p20: schematic led_matrix.kicad_sch, part in row 1, column 2]

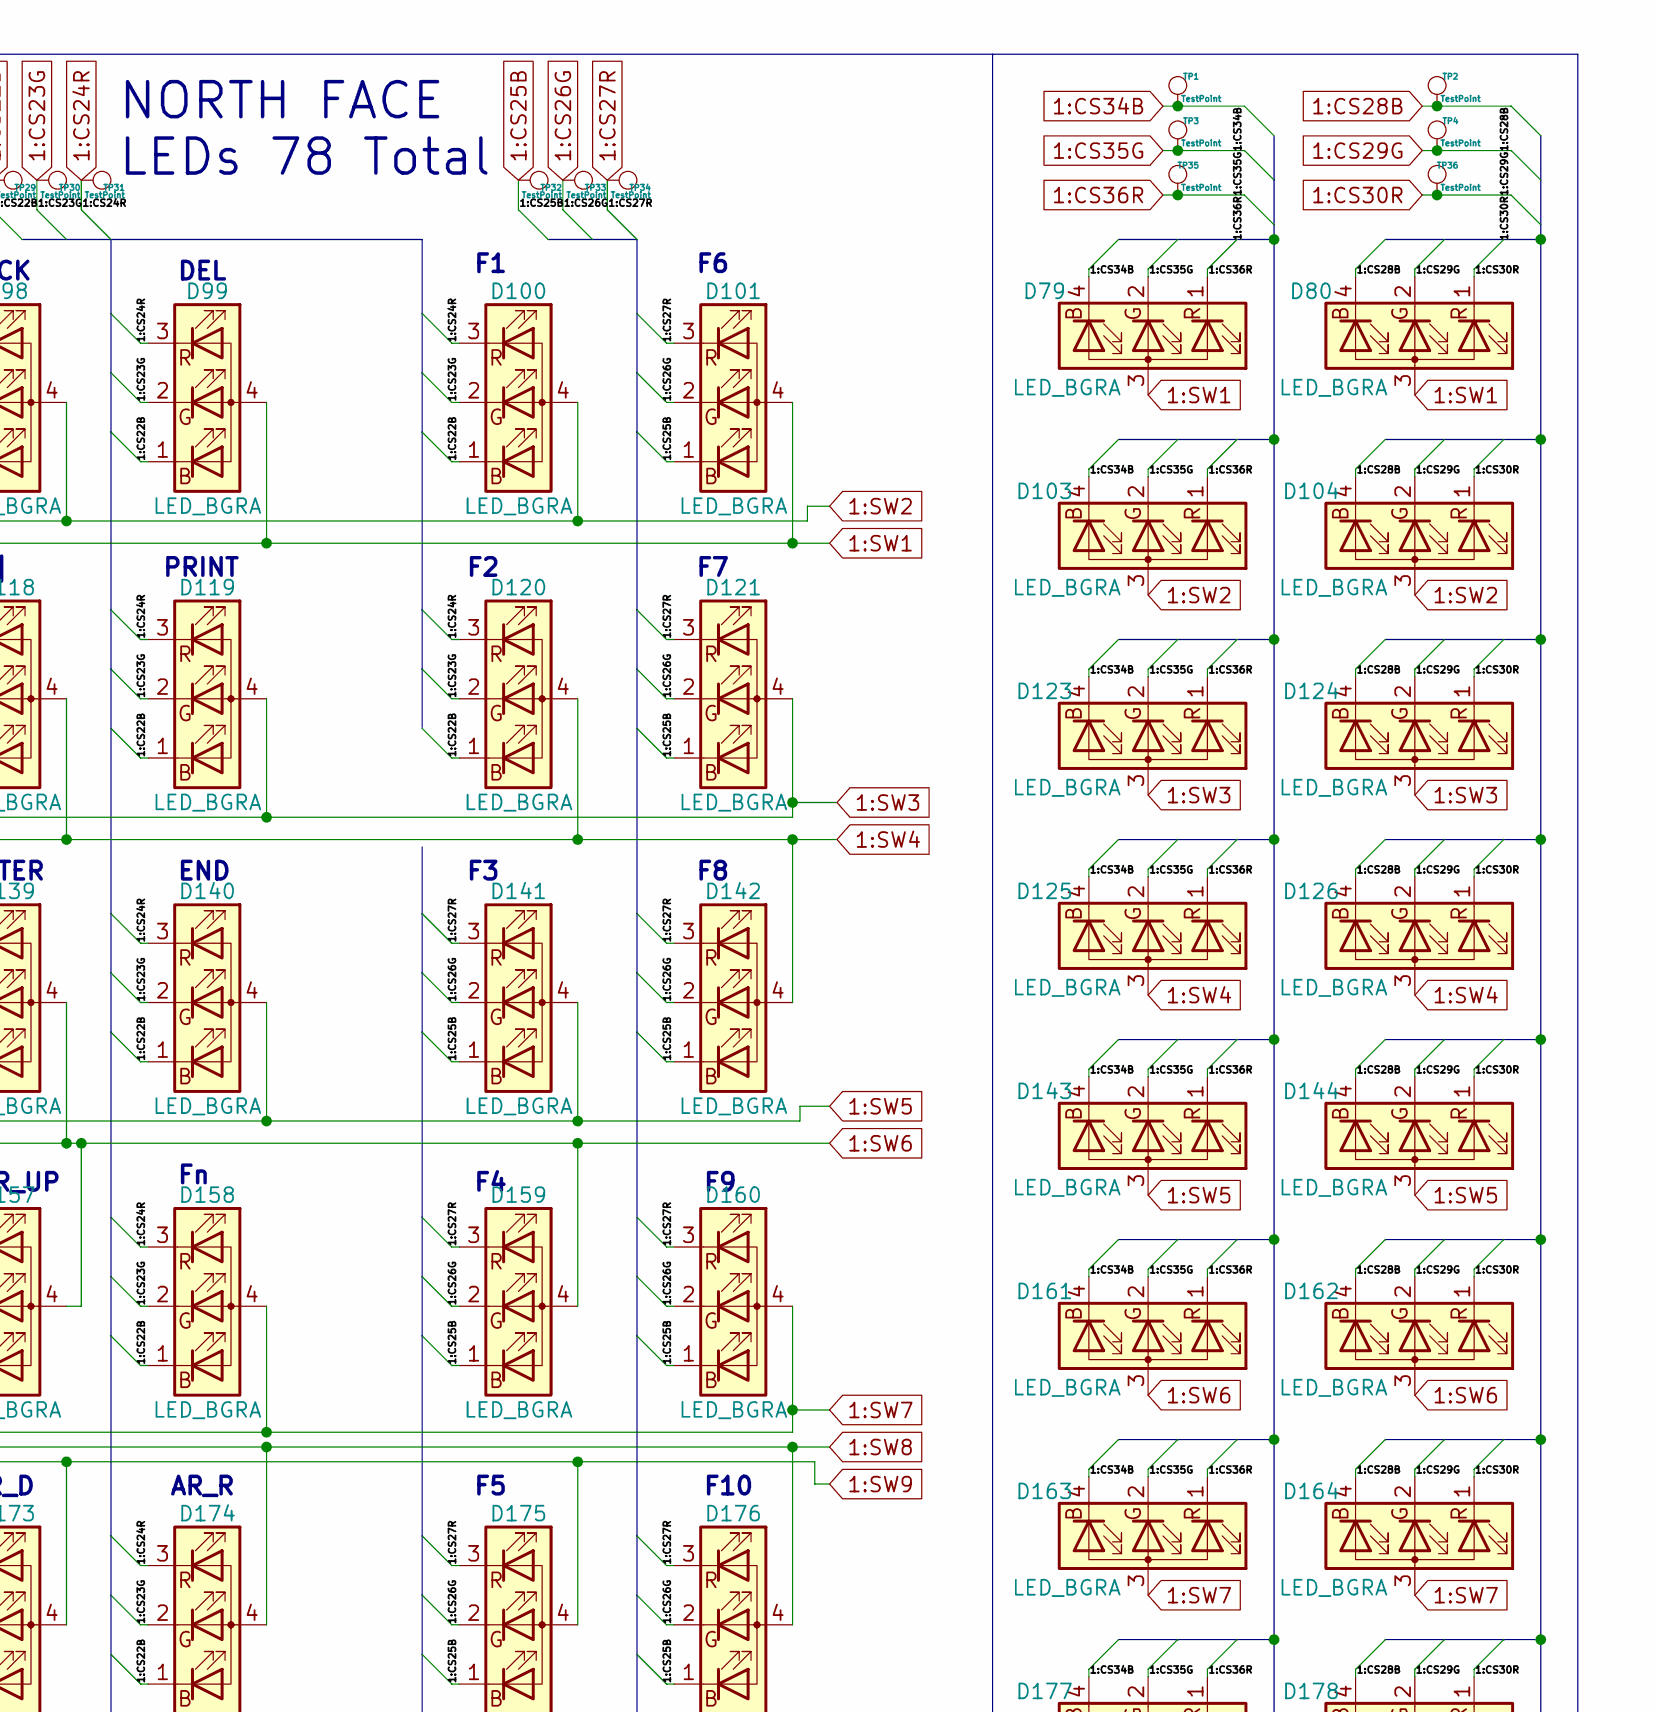
[picture p21: schematic led_matrix.kicad_sch, part in row 1, column 3]

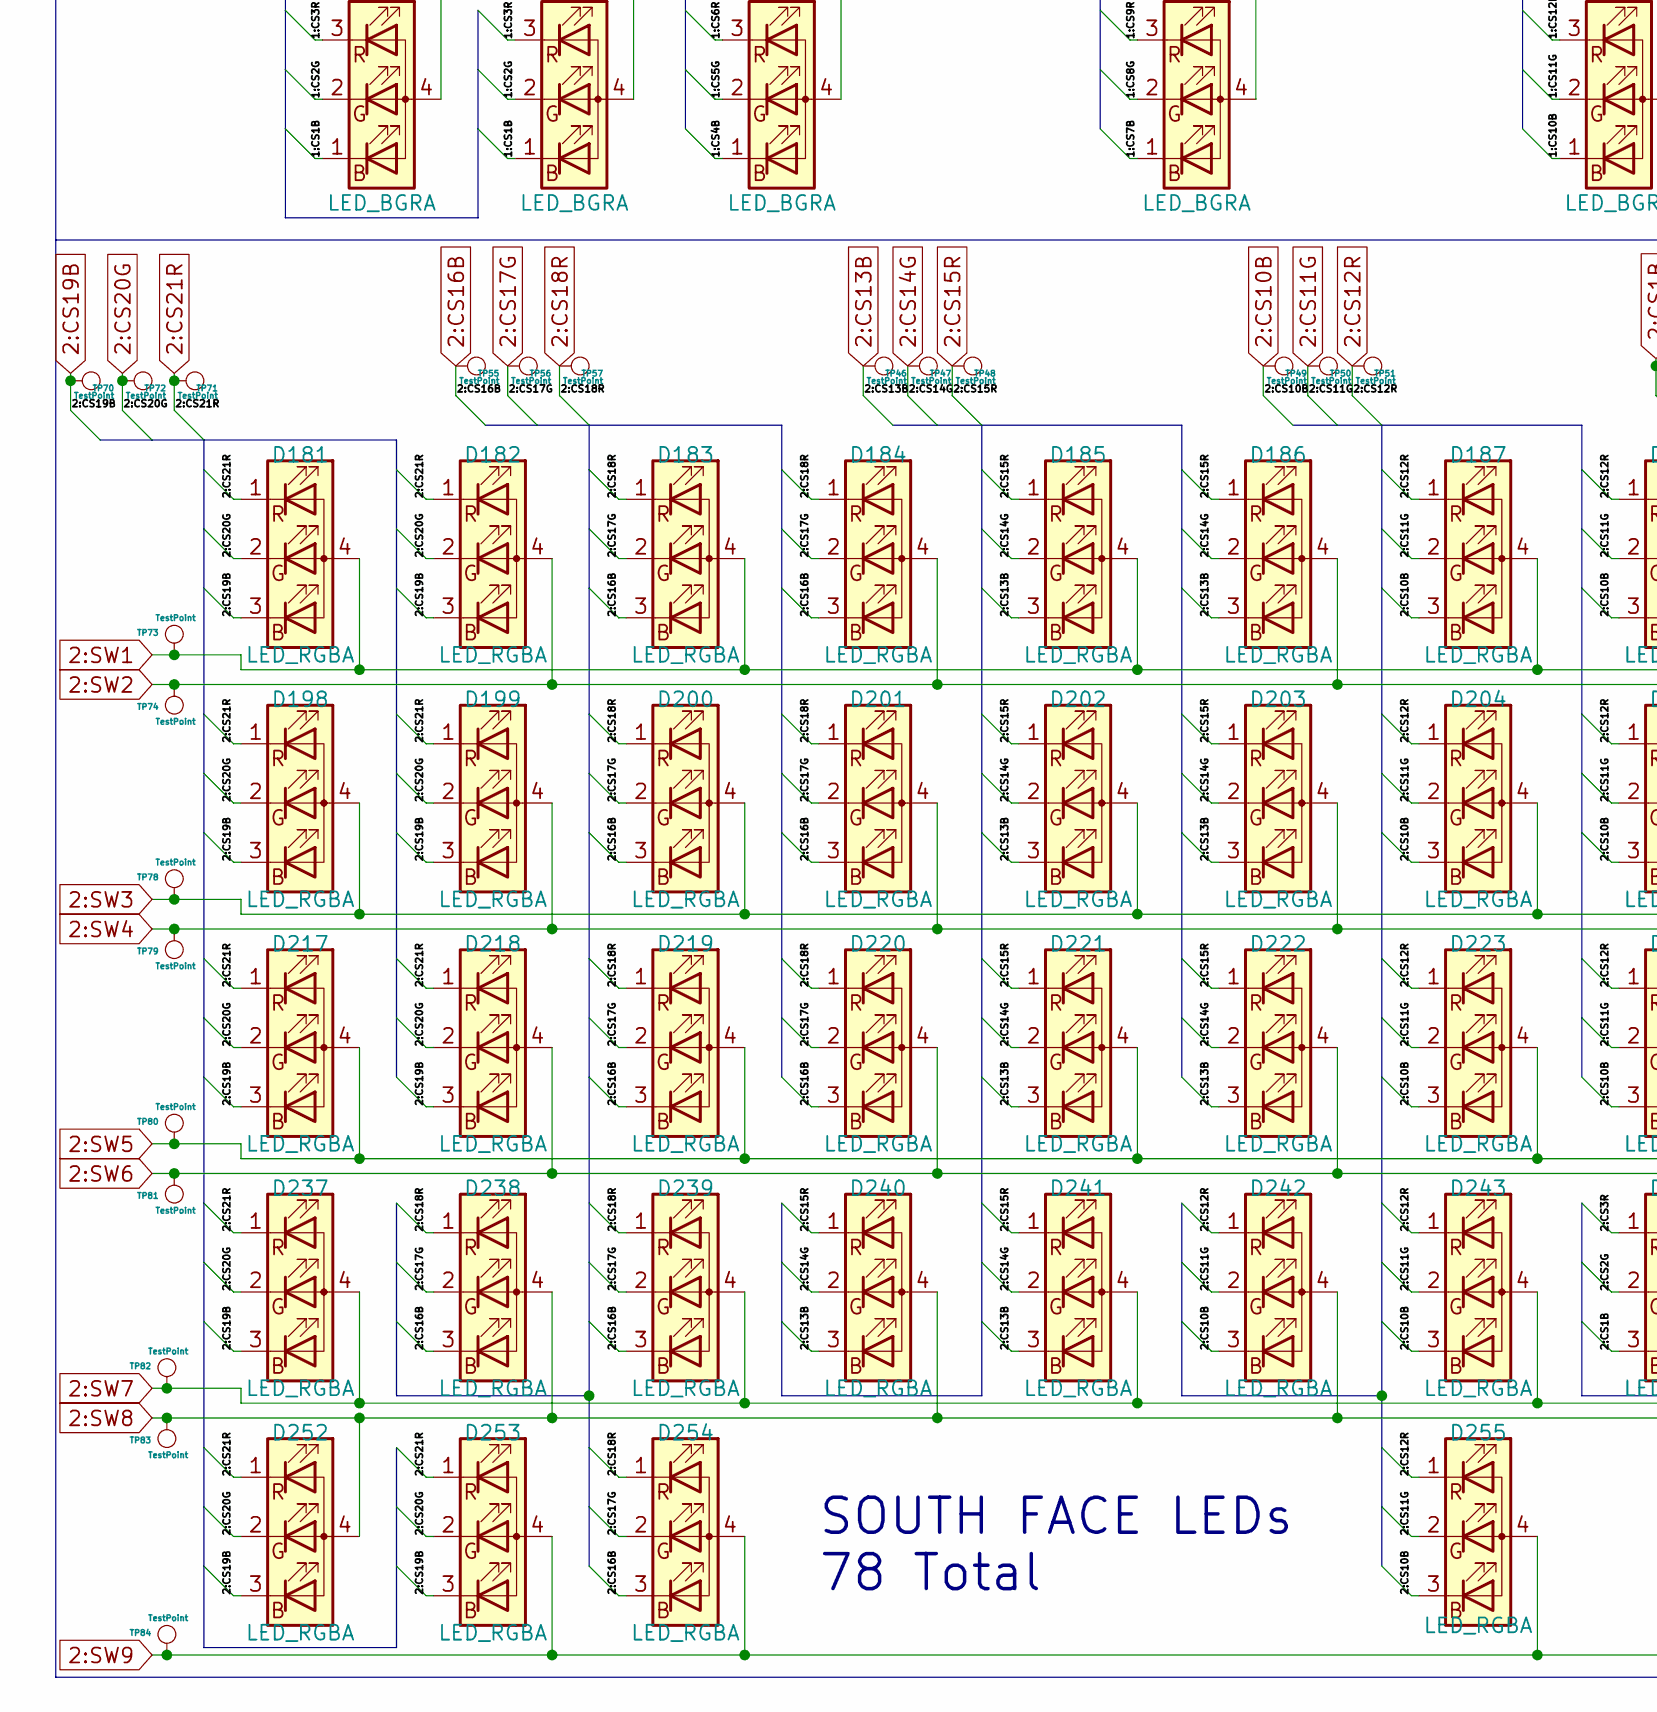
[picture p22: schematic led_matrix.kicad_sch, part in row 2, column 1]

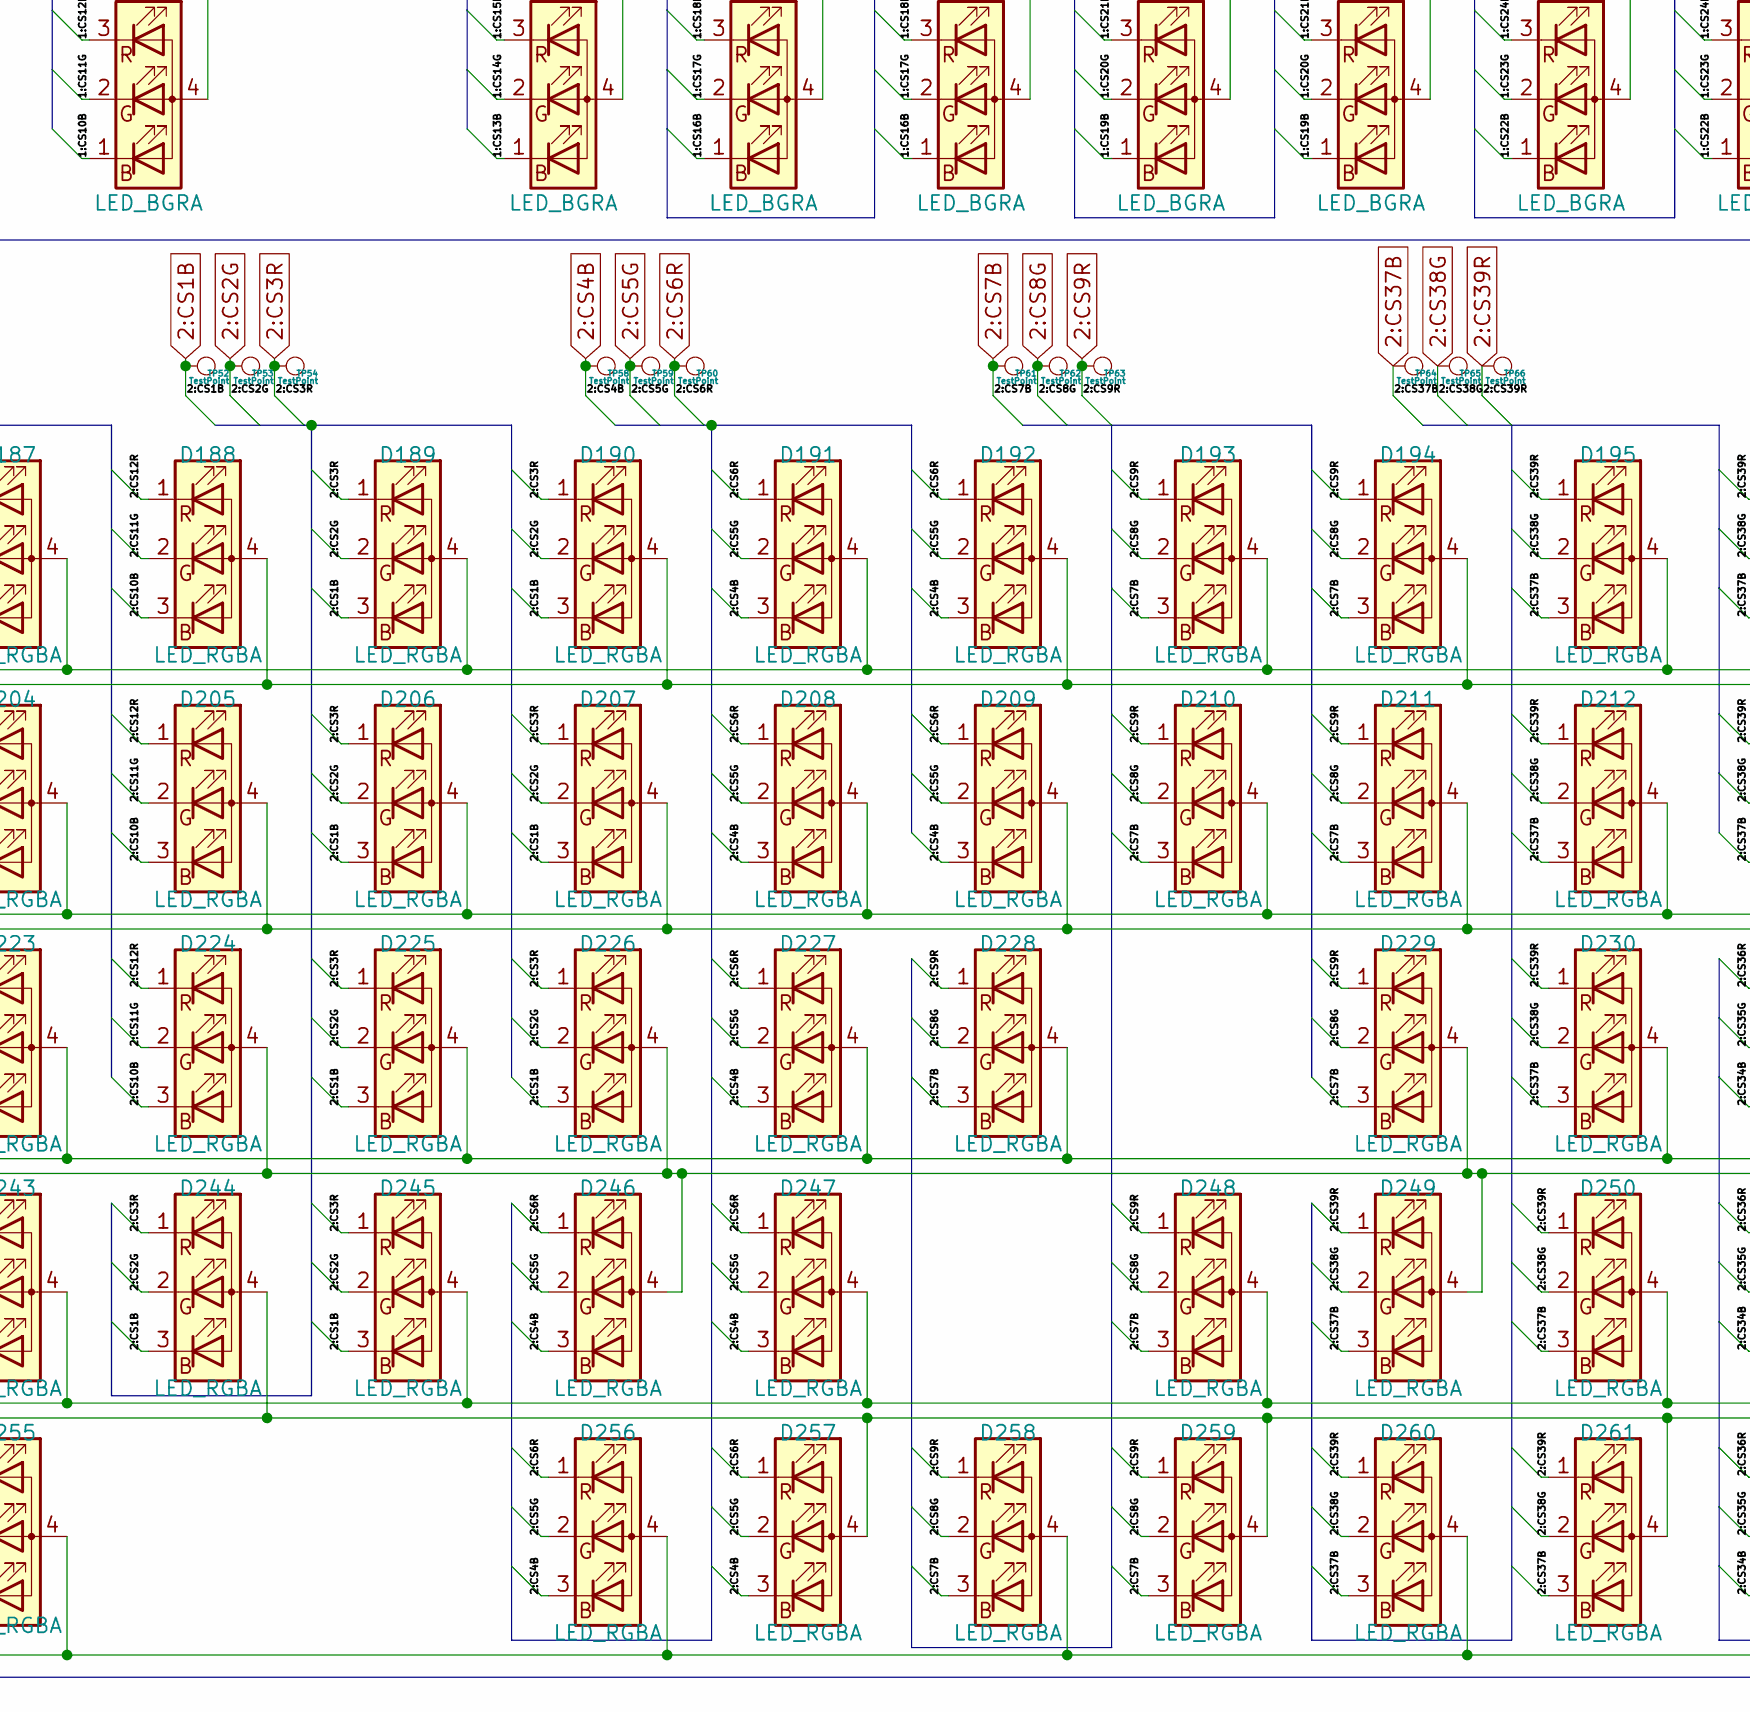
[picture p23: schematic led_matrix.kicad_sch, part in row 2, column 2]

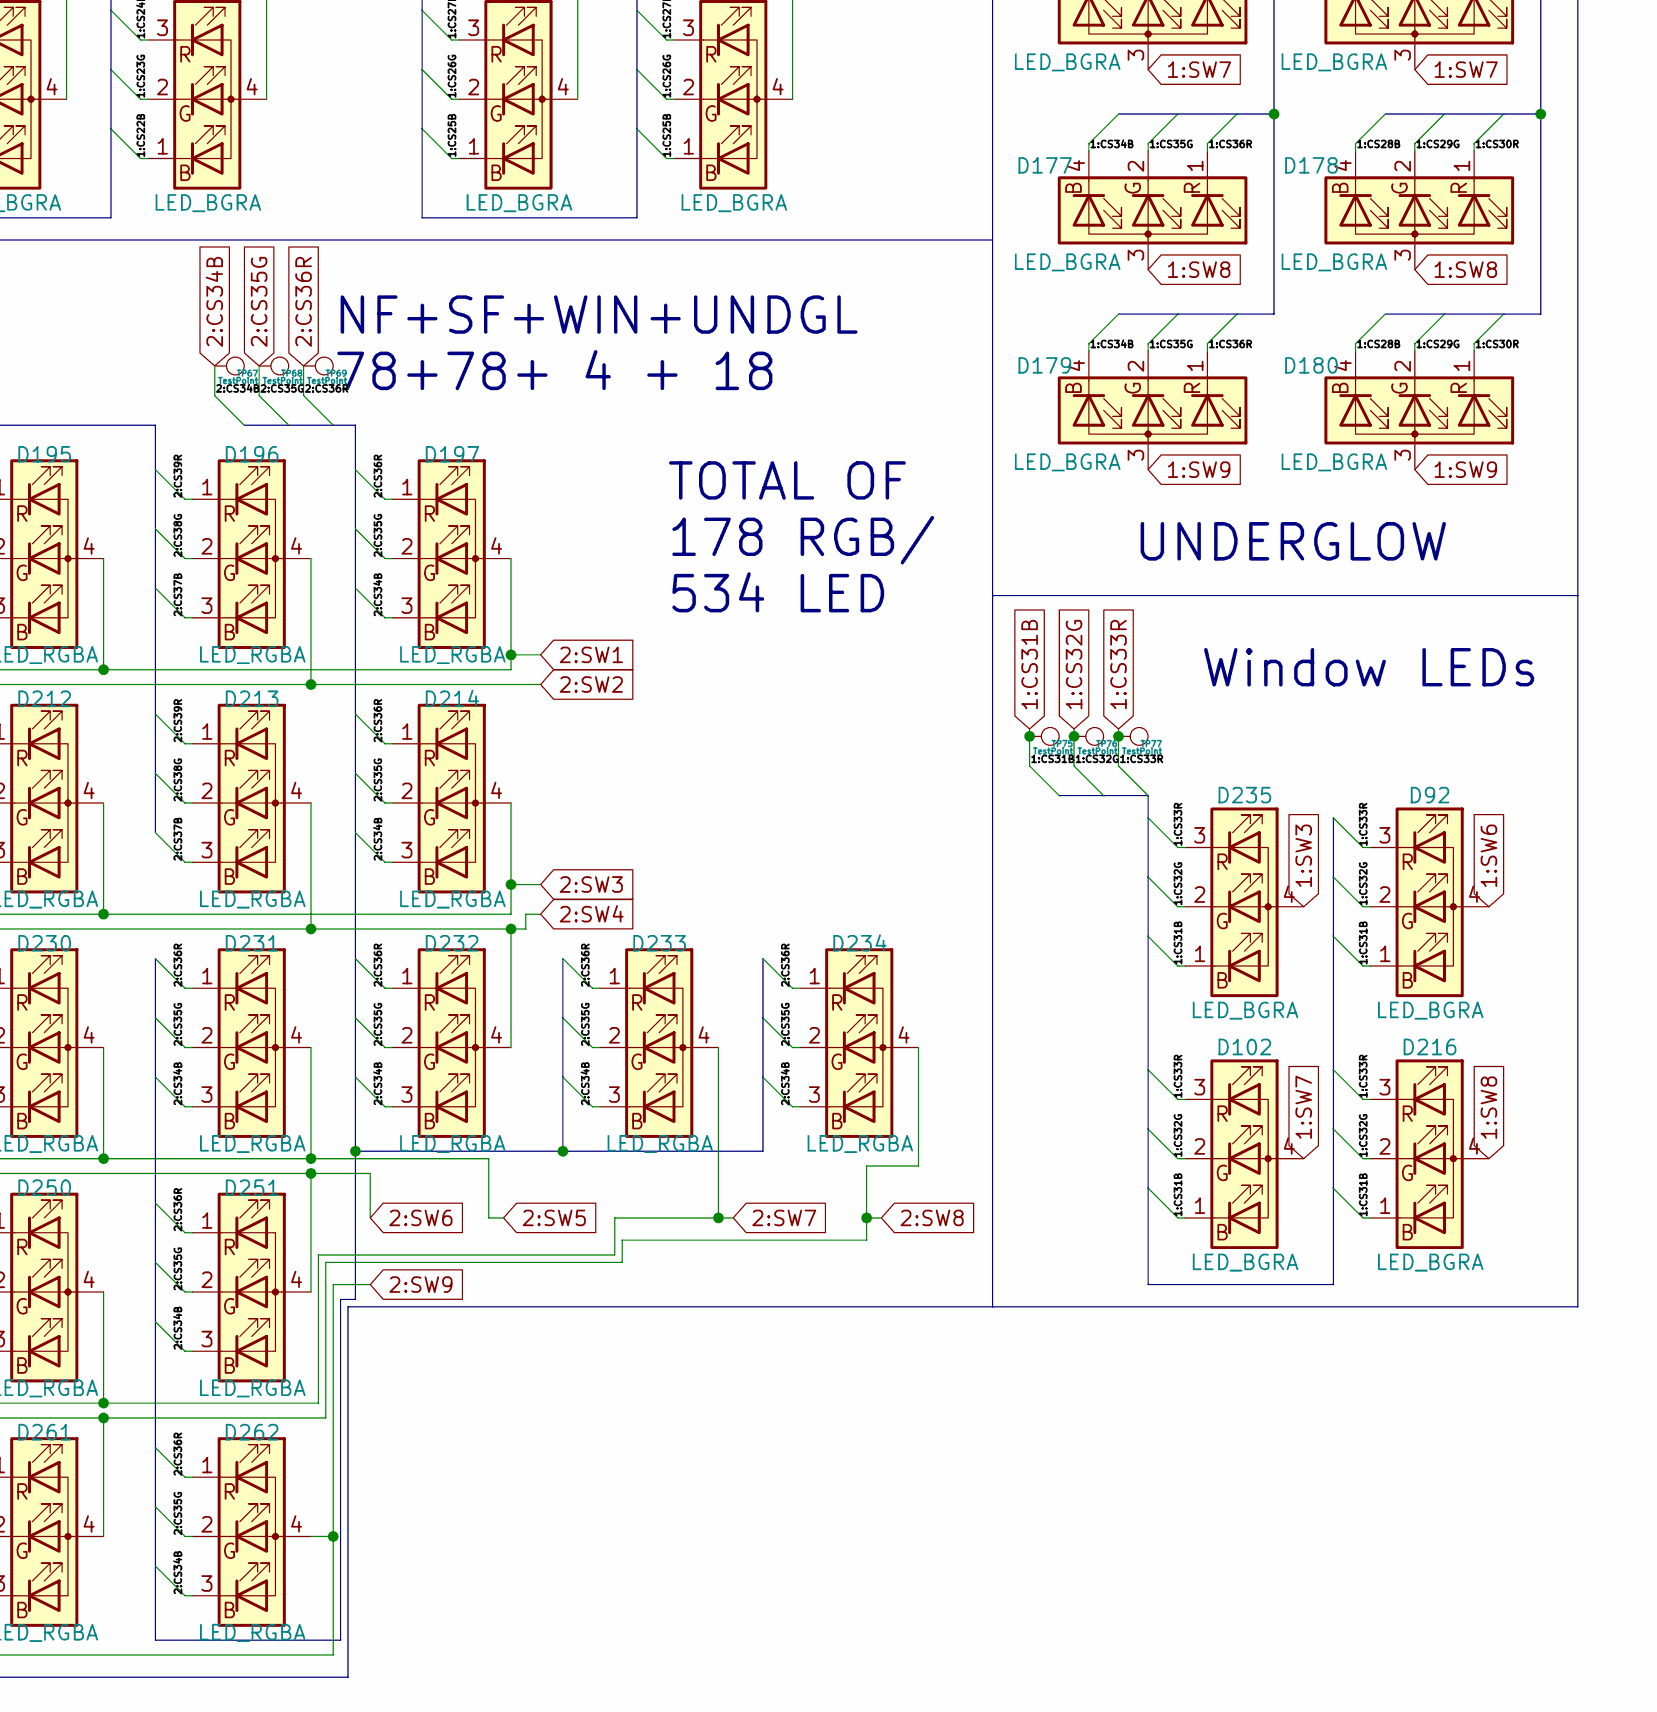
[picture p24: schematic led_matrix.kicad_sch, part in row 2, column 3]

Parts:
D79, D80, D103, D104, D123, D124, D125, D126, D143, D144, D161, D162, D163, D164, D177, D178, D179, D180: LED_BGRA; LED_LTST_FS63HBGED
D81, D82, D83, D84, D85, D86, D87, D88, D89, D90, D92, D95, D96, D97, D98, D99, D100, D101, D102, D105, D106, D107, D108, D109, D110, D111, D112, D113, D114, D115, D116, D117, D118, D119, D120, D121, D127, D128, D129, D130, D131, D132, D133, D134, D135, D136, D137, D138, D139, D140, D141, D142, D145, D146, D147, D148, D149, D150, D151, D152, D153, D154, D155, D156, D157, D158, D159, D160, D165, D166, D167, D168, D169, D170, D171, D172, D173, D174, D175, D176, D216, D235, D263, D264: LED_BGRA; INP32TRRRGB
D181, D182, D183, D184, D185, D186, D187, D188, D189, D190, D191, D192, D193, D194, D195, D196, D197, D198, D199, D200, D201, D202, D203, D204, D205, D206, D207, D208, D209, D210, D211, D212, D213, D214, D217, D218, D219, D220, D221, D222, D223, D224, D225, D226, D227, D228, D229, D230, D231, D232, D233, D234, D237, D238, D239, D240, D241, D242, D243, D244, D245, D246, D247, D248, D249, D250, D251, D252, D253, D254, D255, D256, D257, D258, D259, D260, D261, D262: LED_RGBA; LED_Wurth_0606_1616
TP1, TP2, TP3, TP4, TP5, TP6, TP7, TP8, TP9, TP10, TP11, TP12, TP13, TP14, TP15, TP16, TP17, TP18, TP19, TP20, TP21, TP22, TP26, TP27, TP28, TP29, TP30, TP31, TP32, TP33, TP34, TP35, TP36, TP37, TP38, TP39, TP40, TP41, TP42, TP43, TP44, TP45, TP46, TP47, TP48, TP49, TP50, TP51, TP52, TP53, TP54, TP55, TP56, TP57, TP58, TP59, TP60, TP61, TP62, TP63, TP64, TP65, TP66, TP67, TP68, TP69, TP70, TP71, TP72, TP73, TP74, TP75, TP76, TP77, TP78, TP79, TP80, TP81, TP82, TP83, TP84: TestPoint; TestPoint_Pad_D1.0mm_mini

Connections:
1:CS1B: D81.1 (BK), D82.1 (BK), D105.1 (BK), D106.1 (BK), D127.1 (BK), D128.1 (BK), D145.1 (BK), D165.1 (BK), D166.1 (BK), TP8.1
1:CS2G: D81.2 (GK), D82.2 (GK), D105.2 (GK), D106.2 (GK), D127.2 (GK), D128.2 (GK), D145.2 (GK), D165.2 (GK), D166.2 (GK), TP9.1
1:CS3R: D81.3 (RK), D82.3 (RK), D105.3 (RK), D106.3 (RK), D127.3 (RK), D128.3 (RK), D145.3 (RK), D165.3 (RK), D166.3 (RK), TP5.1
1:CS4B: D83.1 (BK), D84.1 (BK), D107.1 (BK), D108.1 (BK), D129.1 (BK), D130.1 (BK), D146.1 (BK), D147.1 (BK), D167.1 (BK), TP10.1
1:CS5G: D83.2 (GK), D84.2 (GK), D107.2 (GK), D108.2 (GK), D129.2 (GK), D130.2 (GK), D146.2 (GK), D147.2 (GK), D167.2 (GK), TP11.1
1:CS6R: D83.3 (RK), D84.3 (RK), D107.3 (RK), D108.3 (RK), D129.3 (RK), D130.3 (RK), D146.3 (RK), D147.3 (RK), D167.3 (RK), TP6.1
1:CS7B: D85.1 (BK), D86.1 (BK), D109.1 (BK), D110.1 (BK), D131.1 (BK), D132.1 (BK), D148.1 (BK), D149.1 (BK), D263.1 (BK), TP12.1
1:CS8G: D85.2 (GK), D86.2 (GK), D109.2 (GK), D110.2 (GK), D131.2 (GK), D132.2 (GK), D148.2 (GK), D149.2 (GK), D263.2 (GK), TP13.1
1:CS9R: D85.3 (RK), D86.3 (RK), D109.3 (RK), D110.3 (RK), D131.3 (RK), D132.3 (RK), D148.3 (RK), D149.3 (RK), D263.3 (RK), TP7.1
1:CS10B: D87.1 (BK), D88.1 (BK), D111.1 (BK), D112.1 (BK), D133.1 (BK), D134.1 (BK), D150.1 (BK), D151.1 (BK), D168.1 (BK), TP14.1
1:CS11G: D87.2 (GK), D88.2 (GK), D111.2 (GK), D112.2 (GK), D133.2 (GK), D134.2 (GK), D150.2 (GK), D151.2 (GK), D168.2 (GK), TP15.1
1:CS12R: D87.3 (RK), D88.3 (RK), D111.3 (RK), D112.3 (RK), D133.3 (RK), D134.3 (RK), D150.3 (RK), D151.3 (RK), D168.3 (RK), TP16.1
1:CS13B: D89.1 (BK), D90.1 (BK), D113.1 (BK), D114.1 (BK), D135.1 (BK), D136.1 (BK), D152.1 (BK), D153.1 (BK), D264.1 (BK), TP17.1
1:CS14G: D89.2 (GK), D90.2 (GK), D113.2 (GK), D114.2 (GK), D135.2 (GK), D136.2 (GK), D152.2 (GK), D153.2 (GK), D264.2 (GK), TP18.1
1:CS15R: D89.3 (RK), D90.3 (RK), D113.3 (RK), D114.3 (RK), D135.3 (RK), D136.3 (RK), D152.3 (RK), D153.3 (RK), D264.3 (RK), TP19.1
1:CS16B: D95.1 (BK), D96.1 (BK), D115.1 (BK), D116.1 (BK), D137.1 (BK), D154.1 (BK), D155.1 (BK), D169.1 (BK), D170.1 (BK), TP20.1
1:CS17G: D95.2 (GK), D96.2 (GK), D115.2 (GK), D116.2 (GK), D137.2 (GK), D154.2 (GK), D155.2 (GK), D169.2 (GK), D170.2 (GK), TP21.1
1:CS18R: D95.3 (RK), D96.3 (RK), D115.3 (RK), D116.3 (RK), D137.3 (RK), D154.3 (RK), D155.3 (RK), D169.3 (RK), D170.3 (RK), TP22.1
1:CS19B: D97.1 (BK), D98.1 (BK), D117.1 (BK), D118.1 (BK), D138.1 (BK), D139.1 (BK), D156.1 (BK), D171.1 (BK), D172.1 (BK), TP26.1
1:CS20G: D97.2 (GK), D98.2 (GK), D117.2 (GK), D118.2 (GK), D138.2 (GK), D139.2 (GK), D156.2 (GK), D171.2 (GK), D172.2 (GK), TP27.1
1:CS21R: D97.3 (RK), D98.3 (RK), D117.3 (RK), D118.3 (RK), D138.3 (RK), D139.3 (RK), D156.3 (RK), D171.3 (RK), D172.3 (RK), TP28.1
1:CS22B: D99.1 (BK), D100.1 (BK), D119.1 (BK), D120.1 (BK), D140.1 (BK), D157.1 (BK), D158.1 (BK), D173.1 (BK), D174.1 (BK), TP29.1
1:CS23G: D99.2 (GK), D100.2 (GK), D119.2 (GK), D120.2 (GK), D140.2 (GK), D157.2 (GK), D158.2 (GK), D173.2 (GK), D174.2 (GK), TP30.1
1:CS24R: D99.3 (RK), D100.3 (RK), D119.3 (RK), D120.3 (RK), D140.3 (RK), D157.3 (RK), D158.3 (RK), D173.3 (RK), D174.3 (RK), TP31.1
1:CS25B: D101.1 (BK), D121.1 (BK), D141.1 (BK), D142.1 (BK), D159.1 (BK), D160.1 (BK), D175.1 (BK), D176.1 (BK), TP32.1
1:CS26G: D101.2 (GK), D121.2 (GK), D141.2 (GK), D142.2 (GK), D159.2 (GK), D160.2 (GK), D175.2 (GK), D176.2 (GK), TP33.1
1:CS27R: D101.3 (RK), D121.3 (RK), D141.3 (RK), D142.3 (RK), D159.3 (RK), D160.3 (RK), D175.3 (RK), D176.3 (RK), TP34.1
1:CS28B: D80.4 (BK), D104.4 (BK), D124.4 (BK), D126.4 (BK), D144.4 (BK), D162.4 (BK), D164.4 (BK), D178.4 (BK), D180.4 (BK), TP2.1
1:CS29G: D80.2 (GK), D104.2 (GK), D124.2 (GK), D126.2 (GK), D144.2 (GK), D162.2 (GK), D164.2 (GK), D178.2 (GK), D180.2 (GK), TP4.1
1:CS30R: D80.1 (RK), D104.1 (RK), D124.1 (RK), D126.1 (RK), D144.1 (RK), D162.1 (RK), D164.1 (RK), D178.1 (RK), D180.1 (RK), TP36.1
1:CS31B: D92.1 (BK), D102.1 (BK), D216.1 (BK), D235.1 (BK), TP75.1
1:CS32G: D92.2 (GK), D102.2 (GK), D216.2 (GK), D235.2 (GK), TP76.1
1:CS33R: D92.3 (RK), D102.3 (RK), D216.3 (RK), D235.3 (RK), TP77.1
1:CS34B: D79.4 (BK), D103.4 (BK), D123.4 (BK), D125.4 (BK), D143.4 (BK), D161.4 (BK), D163.4 (BK), D177.4 (BK), D179.4 (BK), TP1.1
1:CS35G: D79.2 (GK), D103.2 (GK), D123.2 (GK), D125.2 (GK), D143.2 (GK), D161.2 (GK), D163.2 (GK), D177.2 (GK), D179.2 (GK), TP3.1
1:CS36R: D79.1 (RK), D103.1 (RK), D123.1 (RK), D125.1 (RK), D143.1 (RK), D161.1 (RK), D163.1 (RK), D177.1 (RK), D179.1 (RK), TP35.1
1:SW1: D79.3 (A), D80.3 (A), D81.4 (A), D83.4 (A), D85.4 (A), D87.4 (A), D89.4 (A), D95.4 (A), D97.4 (A), D99.4 (A), D101.4 (A), TP38.1
1:SW2: D82.4 (A), D84.4 (A), D86.4 (A), D88.4 (A), D90.4 (A), D96.4 (A), D98.4 (A), D100.4 (A), D103.3 (A), D104.3 (A), TP37.1
1:SW3: D105.4 (A), D107.4 (A), D109.4 (A), D111.4 (A), D113.4 (A), D115.4 (A), D117.4 (A), D119.4 (A), D121.4 (A), D123.3 (A), D124.3 (A), D235.4 (A), TP39.1
1:SW4: D106.4 (A), D108.4 (A), D110.4 (A), D112.4 (A), D114.4 (A), D116.4 (A), D118.4 (A), D120.4 (A), D125.3 (A), D126.3 (A), D142.4 (A), TP40.1
1:SW5: D127.4 (A), D129.4 (A), D131.4 (A), D133.4 (A), D135.4 (A), D137.4 (A), D138.4 (A), D140.4 (A), D141.4 (A), D143.3 (A), D144.3 (A), TP41.1
1:SW6: D92.4 (A), D128.4 (A), D130.4 (A), D132.4 (A), D134.4 (A), D136.4 (A), D139.4 (A), D154.4 (A), D157.4 (A), D159.4 (A), D161.3 (A), D162.3 (A), TP42.1
1:SW7: D102.4 (A), D145.4 (A), D147.4 (A), D149.4 (A), D151.4 (A), D153.4 (A), D155.4 (A), D156.4 (A), D158.4 (A), D160.4 (A), D163.3 (A), D164.3 (A), TP43.1
1:SW8: D146.4 (A), D148.4 (A), D150.4 (A), D152.4 (A), D165.4 (A), D170.4 (A), D172.4 (A), D174.4 (A), D176.4 (A), D177.3 (A), D178.3 (A), D216.4 (A), TP44.1
1:SW9: D166.4 (A), D167.4 (A), D168.4 (A), D169.4 (A), D171.4 (A), D173.4 (A), D175.4 (A), D179.3 (A), D180.3 (A), D263.4 (A), D264.4 (A), TP45.1
2:CS1B: D189.3 (BK), D190.3 (BK), D206.3 (BK), D207.3 (BK), D225.3 (BK), D226.3 (BK), D244.3 (BK), D245.3 (BK), TP52.1
2:CS2G: D189.2 (GK), D190.2 (GK), D206.2 (GK), D207.2 (GK), D225.2 (GK), D226.2 (GK), D244.2 (GK), D245.2 (GK), TP53.1
2:CS3R: D189.1 (RK), D190.1 (RK), D206.1 (RK), D207.1 (RK), D225.1 (RK), D226.1 (RK), D244.1 (RK), D245.1 (RK), TP54.1
2:CS4B: D191.3 (BK), D192.3 (BK), D208.3 (BK), D209.3 (BK), D227.3 (BK), D246.3 (BK), D247.3 (BK), D256.3 (BK), D257.3 (BK), TP58.1
2:CS5G: D191.2 (GK), D192.2 (GK), D208.2 (GK), D209.2 (GK), D227.2 (GK), D246.2 (GK), D247.2 (GK), D256.2 (GK), D257.2 (GK), TP59.1
2:CS6R: D191.1 (RK), D192.1 (RK), D208.1 (RK), D209.1 (RK), D227.1 (RK), D246.1 (RK), D247.1 (RK), D256.1 (RK), D257.1 (RK), TP60.1
2:CS7B: D193.3 (BK), D194.3 (BK), D210.3 (BK), D211.3 (BK), D228.3 (BK), D229.3 (BK), D248.3 (BK), D258.3 (BK), D259.3 (BK), TP61.1
2:CS8G: D193.2 (GK), D194.2 (GK), D210.2 (GK), D211.2 (GK), D228.2 (GK), D229.2 (GK), D248.2 (GK), D258.2 (GK), D259.2 (GK), TP62.1
2:CS9R: D193.1 (RK), D194.1 (RK), D210.1 (RK), D211.1 (RK), D228.1 (RK), D229.1 (RK), D248.1 (RK), D258.1 (RK), D259.1 (RK), TP63.1
2:CS10B: D187.3 (BK), D188.3 (BK), D204.3 (BK), D205.3 (BK), D223.3 (BK), D224.3 (BK), D242.3 (BK), D243.3 (BK), D255.3 (BK), TP49.1
2:CS11G: D187.2 (GK), D188.2 (GK), D204.2 (GK), D205.2 (GK), D223.2 (GK), D224.2 (GK), D242.2 (GK), D243.2 (GK), D255.2 (GK), TP50.1
2:CS12R: D187.1 (RK), D188.1 (RK), D204.1 (RK), D205.1 (RK), D223.1 (RK), D224.1 (RK), D242.1 (RK), D243.1 (RK), D255.1 (RK), TP51.1
2:CS13B: D185.3 (BK), D186.3 (BK), D202.3 (BK), D203.3 (BK), D221.3 (BK), D222.3 (BK), D240.3 (BK), D241.3 (BK), TP46.1
2:CS14G: D185.2 (GK), D186.2 (GK), D202.2 (GK), D203.2 (GK), D221.2 (GK), D222.2 (GK), D240.2 (GK), D241.2 (GK), TP47.1
2:CS15R: D185.1 (RK), D186.1 (RK), D202.1 (RK), D203.1 (RK), D221.1 (RK), D222.1 (RK), D240.1 (RK), D241.1 (RK), TP48.1
2:CS16B: D183.3 (BK), D184.3 (BK), D200.3 (BK), D201.3 (BK), D219.3 (BK), D220.3 (BK), D238.3 (BK), D239.3 (BK), D254.3 (BK), TP55.1
2:CS17G: D183.2 (GK), D184.2 (GK), D200.2 (GK), D201.2 (GK), D219.2 (GK), D220.2 (GK), D238.2 (GK), D239.2 (GK), D254.2 (GK), TP56.1
2:CS18R: D183.1 (RK), D184.1 (RK), D200.1 (RK), D201.1 (RK), D219.1 (RK), D220.1 (RK), D238.1 (RK), D239.1 (RK), D254.1 (RK), TP57.1
2:CS19B: D181.3 (BK), D182.3 (BK), D198.3 (BK), D199.3 (BK), D217.3 (BK), D218.3 (BK), D237.3 (BK), D252.3 (BK), D253.3 (BK), TP70.1
2:CS20G: D181.2 (GK), D182.2 (GK), D198.2 (GK), D199.2 (GK), D217.2 (GK), D218.2 (GK), D237.2 (GK), D252.2 (GK), D253.2 (GK), TP72.1
2:CS21R: D181.1 (RK), D182.1 (RK), D198.1 (RK), D199.1 (RK), D217.1 (RK), D218.1 (RK), D237.1 (RK), D252.1 (RK), D253.1 (RK), TP71.1
2:CS34B: D197.3 (BK), D214.3 (BK), D231.3 (BK), D232.3 (BK), D233.3 (BK), D234.3 (BK), D251.3 (BK), D262.3 (BK), TP67.1
2:CS35G: D197.2 (GK), D214.2 (GK), D231.2 (GK), D232.2 (GK), D233.2 (GK), D234.2 (GK), D251.2 (GK), D262.2 (GK), TP68.1
2:CS36R: D197.1 (RK), D214.1 (RK), D231.1 (RK), D232.1 (RK), D233.1 (RK), D234.1 (RK), D251.1 (RK), D262.1 (RK), TP69.1
2:CS37B: D195.3 (BK), D196.3 (BK), D212.3 (BK), D213.3 (BK), D230.3 (BK), D249.3 (BK), D250.3 (BK), D260.3 (BK), D261.3 (BK), TP64.1
2:CS38G: D195.2 (GK), D196.2 (GK), D212.2 (GK), D213.2 (GK), D230.2 (GK), D249.2 (GK), D250.2 (GK), D260.2 (GK), D261.2 (GK), TP65.1
2:CS39R: D195.1 (RK), D196.1 (RK), D212.1 (RK), D213.1 (RK), D230.1 (RK), D249.1 (RK), D250.1 (RK), D260.1 (RK), D261.1 (RK), TP66.1
2:SW1: D181.4 (A), D183.4 (A), D185.4 (A), D187.4 (A), D189.4 (A), D191.4 (A), D193.4 (A), D195.4 (A), D197.4 (A), TP73.1
2:SW2: D182.4 (A), D184.4 (A), D186.4 (A), D188.4 (A), D190.4 (A), D192.4 (A), D194.4 (A), D196.4 (A), TP74.1
2:SW3: D198.4 (A), D200.4 (A), D202.4 (A), D204.4 (A), D206.4 (A), D208.4 (A), D210.4 (A), D212.4 (A), D214.4 (A), TP78.1
2:SW4: D199.4 (A), D201.4 (A), D203.4 (A), D205.4 (A), D207.4 (A), D209.4 (A), D211.4 (A), D213.4 (A), D232.4 (A), TP79.1
2:SW5: D217.4 (A), D219.4 (A), D221.4 (A), D223.4 (A), D225.4 (A), D227.4 (A), D228.4 (A), D230.4 (A), D231.4 (A), TP80.1
2:SW6: D218.4 (A), D220.4 (A), D222.4 (A), D224.4 (A), D226.4 (A), D229.4 (A), D246.4 (A), D249.4 (A), D251.4 (A), TP81.1
2:SW7: D233.4 (A), D237.4 (A), D239.4 (A), D241.4 (A), D243.4 (A), D245.4 (A), D247.4 (A), D248.4 (A), D250.4 (A), TP82.1
2:SW8: D234.4 (A), D238.4 (A), D240.4 (A), D242.4 (A), D244.4 (A), D252.4 (A), D257.4 (A), D259.4 (A), D261.4 (A), TP83.1
2:SW9: D253.4 (A), D254.4 (A), D255.4 (A), D256.4 (A), D258.4 (A), D260.4 (A), D262.4 (A), TP84.1

Notes on the sheet:
SPACE
F10
NF+SF+WIN+UNDGL 78+78+ 4 + 18
SHIFT_L
SPACE JP
Window LEDs
BACK
WIN
CAPS
AR_R
ENTER
AR_L
AR_D
DEL
ALT_L
CTRL_R
NORTH FACE LEDs 78 Total
SPACE DE
SHIFT_R
TOTAL OF 178 RGB/ 534 LED
PRINT
ESC
KANA
END
TAB
UNDERGLOW
CTRL_L
AR_UP
ALT_R
SOUTH FACE LEDs 78 Total
